Areeeeen/OW_Signalscope_Planet_Finder/firmware/v2.0/Signalscope_v2.0/astronomy.c

/*
    Astronomy Engine for C/C++.
    https://github.com/cosinekitty/astronomy

    MIT License

    Copyright (c) 2019-2025 Don Cross <cosinekitty@gmail.com>

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
    THE SOFTWARE IS PROVIDED "AS IS", WITHOUT WARRANTY OF ANY KIND, EXPRESS OR
    IMPLIED, INCLUDING BUT NOT LIMITED TO THE WARRANTIES OF MERCHANTABILITY,
    FITNESS FOR A PARTICULAR PURPOSE AND NONINFRINGEMENT. IN NO EVENT SHALL THE
    AUTHORS OR COPYRIGHT HOLDERS BE LIABLE FOR ANY CLAIM, DAMAGES OR OTHER
    LIABILITY, WHETHER IN AN ACTION OF CONTRACT, TORT OR OTHERWISE, ARISING FROM,
    OUT OF OR IN CONNECTION WITH THE SOFTWARE OR THE USE OR OTHER DEALINGS IN THE
    SOFTWARE.
*/

#include <math.h>
#include <stdint.h>
#include <stdio.h>
#include <stdlib.h>
#include <string.h>

#define ASTRONOMY_ENGINE_WHOLE_SECOND

#if !defined(ASTRONOMY_ENGINE_NO_CURRENT_TIME)
#if defined(__unix__) || defined(__unix) || (defined(__APPLE__) && defined(__MACH__))
#include <sys/time.h>
#elif defined(_WIN32)
#define WIN32_LEAN_AND_MEAN
#include <windows.h>
#else
#include <time.h>
#endif
#endif

#include "astronomy.h"

#ifdef __FAST_MATH__
#error Astronomy Engine does not support "fast math" optimization because it causes incorrect behavior. See: https://github.com/cosinekitty/astronomy/issues/245
#endif

#ifdef __cplusplus
extern "C" {
#endif

/** @cond DOXYGEN_SKIP */
#define PI      3.14159265358979323846

#define PLUTO_NUM_STATES  51
#define PLUTO_TIME_STEP   29200
#define PLUTO_DT          146

#define PLUTO_NSTEPS      201



typedef enum
{
    FROM_2000,
    INTO_2000
}
precess_dir_t;

typedef struct
{
    double x;
    double y;
    double z;
}
terse_vector_t;

typedef struct
{
    double          tt;   /* J2000 terrestrial time [days] */
    terse_vector_t  r;    /* position [au] */
    terse_vector_t  v;    /* velocity [au/day] */
    terse_vector_t  a;    /* acceleration [au/day^2] */
}
body_grav_calc_t;

typedef struct
{
    body_grav_calc_t   step[PLUTO_NSTEPS];
}
body_segment_t;

typedef struct
{
    double          tt;  /* Terrestrial Time in J2000 days */
    terse_vector_t  r;   /* position [au] */
    terse_vector_t  v;   /* velocity [au/day] */
}
body_state_t;

typedef struct
{
    body_state_t Sun;
    body_state_t Jupiter;
    body_state_t Saturn;
    body_state_t Uranus;
    body_state_t Neptune;
}
major_bodies_t;

typedef struct
{
    astro_time_t      time;
    body_state_t      gravitators[1 + BODY_SUN];
    body_grav_calc_t *bodies;
}
gravsim_endpoint_t;

struct astro_grav_sim_s
{
    astro_body_t        originBody;
    int                 numBodies;
    gravsim_endpoint_t  endpoint[2];
    gravsim_endpoint_t *prev;
    gravsim_endpoint_t *curr;
};

typedef struct
{
    double ra;
    double dec;
    double dist;
}
stardef_t;

/* Mean obliquity of the J2000 ecliptic in radians. */
#define OBLIQ_2000       0.40909260059599012
#define COS_OBLIQ_2000   0.9174821430670688
#define SIN_OBLIQ_2000   0.3977769691083922

/** @endcond */

#define NSTARS 8
static stardef_t StarTable[NSTARS];

#define GetStarPointer(body)    (((body) >= BODY_STAR1) && ((body) <= BODY_STAR8) ? &StarTable[(body) - BODY_STAR1] : NULL)

static const stardef_t *UserDefinedStar(astro_body_t body)
{
    const stardef_t *star = GetStarPointer(body);
    if (star != NULL && star->dist > 0.0)
        return star;
    return NULL;
}


/**
 * @brief Assign equatorial coordinates to a user-defined star.
 *
 * Some Astronomy Engine functions allow their `body` parameter to
 * be a user-defined fixed point in the sky, loosely called a "star".
 * This function assigns a right ascension, declination, and distance
 * to one of the eight user-defined stars `BODY_STAR1` .. `BODY_STAR8`.
 *
 * Stars are not valid until defined. Once defined, they retain their
 * definition until re-defined by another call to `Astronomy_DefineStar`.
 *
 * @param body
 *      One of the eight user-defined star identifiers: `BODY_STAR1` .. `BODY_STAR8`.
 *
 * @param ra
 *      The right ascension to be assigned to the star, expressed in J2000 equatorial coordinates (EQJ).
 *      The value is in units of sidereal hours, and must be within the half-open range [0, 24).
 *
 * @param dec
 *      The declination to be assigned to the star, expressed in J2000 equatorial coordinates (EQJ).
 *      The value is in units of degrees north (positive) or south (negative) of the J2000 equator,
 *      and must be within the closed range [-90, +90].
 *
 * @param distanceLightYears
 *      The distance between the star and the Sun, expressed in light-years.
 *      This value is used to calculate the tiny parallax shift as seen by an observer on Earth.
 *      If you don't know the distance to the star, using a large value like 1000 will generally work well.
 *      The minimum allowed distance is 1 light-year, which is required to provide certain internal optimizations.
 *
 * @return
 *      `ASTRO_SUCCESS` indicates the star has been defined. Any other value indicates an error,
 *      in which case no change has taken place to any of the star definitions.
 */
astro_status_t Astronomy_DefineStar(astro_body_t body, double ra, double dec, double distanceLightYears)
{
    stardef_t *star = GetStarPointer(body);

    if (star == NULL)
        return ASTRO_INVALID_BODY;

    if (!isfinite(ra) || ra < 0.0 || ra >= 24.0)
        return ASTRO_INVALID_PARAMETER;

    if (!isfinite(dec) || dec < -90.0 || dec > +90.0)
        return ASTRO_INVALID_PARAMETER;

    if (!isfinite(distanceLightYears) || distanceLightYears < 1.0)
        return ASTRO_INVALID_PARAMETER;

    star->ra   = ra;
    star->dec  = dec;
    star->dist = distanceLightYears * AU_PER_LY;

    return ASTRO_SUCCESS;
}

static const terse_vector_t VecZero = { 0.0, 0.0, 0.0 };

static terse_vector_t VecAdd(terse_vector_t a, terse_vector_t b)
{
    terse_vector_t c;
    c.x = a.x + b.x;
    c.y = a.y + b.y;
    c.z = a.z + b.z;
    return c;
}

static void VecIncr(terse_vector_t *target, terse_vector_t source)
{
    target->x += source.x;
    target->y += source.y;
    target->z += source.z;
}

static void VecDecr(terse_vector_t *target, terse_vector_t source)
{
    target->x -= source.x;
    target->y -= source.y;
    target->z -= source.z;
}

static terse_vector_t VecMul(double s, terse_vector_t v)
{
    terse_vector_t p;
    p.x = s * v.x;
    p.y = s * v.y;
    p.z = s * v.z;
    return p;
}

static void VecScale(terse_vector_t *target, double scalar)
{
    target->x *= scalar;
    target->y *= scalar;
    target->z *= scalar;
}

static terse_vector_t VecRamp(terse_vector_t a, terse_vector_t b, double ramp)
{
    terse_vector_t c;
    c.x = (1-ramp)*a.x + ramp*b.x;
    c.y = (1-ramp)*a.y + ramp*b.y;
    c.z = (1-ramp)*a.z + ramp*b.z;
    return c;
}

static terse_vector_t VecMean(terse_vector_t a, terse_vector_t b)
{
    terse_vector_t c;
    c.x = (a.x + b.x) / 2;
    c.y = (a.y + b.y) / 2;
    c.z = (a.z + b.z) / 2;
    return c;
}

static astro_state_vector_t ExportState(body_state_t terse, astro_time_t time)
{
    astro_state_vector_t state;

    state.status = ASTRO_SUCCESS;
    state.x  = terse.r.x;
    state.y  = terse.r.y;
    state.z  = terse.r.z;
    state.vx = terse.v.x;
    state.vy = terse.v.y;
    state.vz = terse.v.z;
    state.t  = time;

    return state;
}

static astro_state_vector_t ExportGravCalc(body_grav_calc_t calc, astro_time_t time)
{
    astro_state_vector_t state;

    state.status = ASTRO_SUCCESS;
    state.x  = calc.r.x;
    state.y  = calc.r.y;
    state.z  = calc.r.z;
    state.vx = calc.v.x;
    state.vy = calc.v.y;
    state.vz = calc.v.z;
    state.t  = time;

    return state;
}

static const double DAYS_PER_TROPICAL_YEAR = 365.24217;
static const double ASEC360 = 1296000.0;
static const double ASEC2RAD = 4.848136811095359935899141e-6;
static const double PI2 = 2.0 * PI;
static const double ARC = 3600.0 * 180.0 / PI;          /* arcseconds per radian */
static const double SECONDS_PER_DAY = 24.0 * 3600.0;
static const double SOLAR_DAYS_PER_SIDEREAL_DAY = 0.9972695717592592;
static const double MEAN_SYNODIC_MONTH = 29.530588;     /* average number of days for Moon to return to the same phase */
static const double EARTH_ORBITAL_PERIOD = 365.256;
static const double NEPTUNE_ORBITAL_PERIOD = 60189.0;

/*
    Degrees of refractive "lift" seen for objects near horizon.
    More precisely, the angle below the horizon a point has to be, at sea level,
    to appear to be exactly on the horizon.
    If the ground plane is higher than sea level, this angle
    needs to be corrected for decreased atmospheric density.
*/
static const double REFRACTION_NEAR_HORIZON = 34.0 / 60.0;


#define             SUN_RADIUS_AU  (SUN_RADIUS_KM / KM_PER_AU)

#define EARTH_MEAN_RADIUS_KM        6371.0            /* mean radius of the Earth's geoid, without atmosphere */
#define EARTH_ATMOSPHERE_KM           88.0            /* effective atmosphere thickness for lunar eclipses. see: https://eclipse.gsfc.nasa.gov/LEcat5/shadow.html */
#define EARTH_ECLIPSE_RADIUS_KM     (EARTH_MEAN_RADIUS_KM + EARTH_ATMOSPHERE_KM)
#define EARTH_EQUATORIAL_RADIUS_AU  (EARTH_EQUATORIAL_RADIUS_KM / KM_PER_AU)

#define MOON_MEAN_RADIUS_KM         1737.4
#define MOON_EQUATORIAL_RADIUS_AU   (MOON_EQUATORIAL_RADIUS_KM / KM_PER_AU)
#define MOON_POLAR_RADIUS_AU        (MOON_POLAR_RADIUS_KM / KM_PER_AU)

/* The inclination of the moon's rotation axis to the ecliptic plane, in radians. */
#define MOON_AXIS_INCLINATION_RADIANS    (DEG2RAD * 1.543)

static const double ASEC180 = 180.0 * 60.0 * 60.0;      /* arcseconds per 180 degrees (or pi radians) */
static const double EARTH_MOON_MASS_RATIO = 81.30056;

/*
    Masses of the Sun and planets, used for:
    (1) Calculating the Solar System Barycenter
    (2) Integrating the movement of Pluto

    https://web.archive.org/web/20120220062549/http://iau-comm4.jpl.nasa.gov/de405iom/de405iom.pdf

    Page 10 in the above document describes the constants used in the DE405 ephemeris.
    The following are GM values (gravity constant * mass) in [au^3 / day^2].
    This side-steps issues of not knowing the exact values of G and masses M[i];
    the products GM[i] are known extremely accurately.
*/
static const double SUN_GM     = 0.2959122082855911e-03;
static const double MERCURY_GM = 0.4912547451450812e-10;
static const double VENUS_GM   = 0.7243452486162703e-09;
static const double EARTH_GM   = 0.8887692390113509e-09;
static const double MARS_GM    = 0.9549535105779258e-10;
static const double JUPITER_GM = 0.2825345909524226e-06;
static const double SATURN_GM  = 0.8459715185680659e-07;
static const double URANUS_GM  = 0.1292024916781969e-07;
static const double NEPTUNE_GM = 0.1524358900784276e-07;
static const double PLUTO_GM   = 0.2188699765425970e-11;

#define MOON_GM   (EARTH_GM / EARTH_MOON_MASS_RATIO)

/** @cond DOXYGEN_SKIP */
#define ASTRO_ARRAYSIZE(x)    (sizeof(x) / sizeof(x[0]))
#define AU_PER_PARSEC   (ASEC180 / PI)             /* exact definition of how many AU = one parsec */
#define Y2000_IN_MJD    (T0 - MJD_BASIS)
/** @endcond */

static astro_ecliptic_t RotateEquatorialToEcliptic(const double pos[3], double obliq_radians, astro_time_t time);
static int QuadInterp(
    double tm, double dt, double fa, double fm, double fb,
    double *t, double *df_dt);

static double LongitudeOffset(double diff)
{
    double offset = diff;

    while (offset <= -180.0)
        offset += 360.0;

    while (offset > 180.0)
        offset -= 360.0;

    return offset;
}

static double NormalizeLongitude(double lon)
{
    while (lon < 0.0)
        lon += 360.0;

    while (lon >= 360.0)
        lon -= 360.0;

    return lon;
}

/**
 * @brief Calculates the length of the given vector.
 *
 * Calculates the non-negative length of the given vector.
 * The length is expressed in the same units as the vector's components,
 * usually astronomical units (AU).
 *
 * @param vector The vector whose length is to be calculated.
 * @return The length of the vector.
 */
double Astronomy_VectorLength(astro_vector_t vector)
{
    return sqrt(vector.x*vector.x + vector.y*vector.y + vector.z*vector.z);
}

/**
 * @brief Finds the name of a celestial body.
 * @param body The celestial body whose name is to be found.
 * @return The English-language name of the celestial body, or "" if the body is not valid.
 */
const char *Astronomy_BodyName(astro_body_t body)
{
    switch (body)
    {
    case BODY_MERCURY:  return "Mercury";
    case BODY_VENUS:    return "Venus";
    case BODY_EARTH:    return "Earth";
    case BODY_MARS:     return "Mars";
    case BODY_JUPITER:  return "Jupiter";
    case BODY_SATURN:   return "Saturn";
    case BODY_URANUS:   return "Uranus";
    case BODY_NEPTUNE:  return "Neptune";
    case BODY_PLUTO:    return "Pluto";
    case BODY_SUN:      return "Sun";
    case BODY_MOON:     return "Moon";
    case BODY_EMB:      return "EMB";
    case BODY_SSB:      return "SSB";
    default:            return "";
    }
}

/**
 * @brief Returns the #astro_body_t value corresponding to the given English name.
 * @param name One of the following strings: Sun, Moon, Mercury, Venus, Earth, Mars, Jupiter, Saturn, Uranus, Neptune, Pluto, EMB, SSB.
 * @return If `name` is one of the listed strings (case-sensitive), the returned value is the corresponding #astro_body_t value, otherwise it is `BODY_INVALID`.
 */
astro_body_t Astronomy_BodyCode(const char *name)
{
    if (name != NULL)
    {
        if (!strcmp(name, "Mercury"))   return BODY_MERCURY;
        if (!strcmp(name, "Venus"))     return BODY_VENUS;
        if (!strcmp(name, "Earth"))     return BODY_EARTH;
        if (!strcmp(name, "Mars"))      return BODY_MARS;
        if (!strcmp(name, "Jupiter"))   return BODY_JUPITER;
        if (!strcmp(name, "Saturn"))    return BODY_SATURN;
        if (!strcmp(name, "Uranus"))    return BODY_URANUS;
        if (!strcmp(name, "Neptune"))   return BODY_NEPTUNE;
        if (!strcmp(name, "Pluto"))     return BODY_PLUTO;
        if (!strcmp(name, "Sun"))       return BODY_SUN;
        if (!strcmp(name, "Moon"))      return BODY_MOON;
        if (!strcmp(name, "EMB"))       return BODY_EMB;
        if (!strcmp(name, "SSB"))       return BODY_SSB;
    }
    return BODY_INVALID;
}

/**
 * @brief Returns 1 for planets that are farther from the Sun than the Earth is, 0 otherwise.
 */
static int IsSuperiorPlanet(astro_body_t body)
{
    switch (body)
    {
    case BODY_MARS:
    case BODY_JUPITER:
    case BODY_SATURN:
    case BODY_URANUS:
    case BODY_NEPTUNE:
    case BODY_PLUTO:
        return 1;

    default:
        return 0;
    }
}

/**
 * @brief Returns the average number of days it takes for a planet to orbit the Sun.
 * @param body One of the planets: Mercury, Venus, Earth, Mars, Jupiter, Saturn, Uranus, Neptune, or Pluto.
 * @return The mean orbital period of the body, or 0.0 if the `body` parameter is not valid.
 */
double Astronomy_PlanetOrbitalPeriod(astro_body_t body)
{
    switch (body)
    {
    case BODY_MERCURY:  return     87.969;
    case BODY_VENUS:    return    224.701;
    case BODY_EARTH:    return    EARTH_ORBITAL_PERIOD;
    case BODY_MARS:     return    686.980;
    case BODY_JUPITER:  return   4332.589;
    case BODY_SATURN:   return  10759.22;
    case BODY_URANUS:   return  30685.4;
    case BODY_NEPTUNE:  return  NEPTUNE_ORBITAL_PERIOD;
    case BODY_PLUTO:    return  90560.0;
    default:            return  0.0;        /* invalid body */
    }
}

static astro_vector_t VecError(astro_status_t status, astro_time_t time)
{
    astro_vector_t vec;
    vec.x = vec.y = vec.z = NAN;
    vec.t = time;
    vec.status = status;
    return vec;
}

static astro_state_vector_t StateVecError(astro_status_t status, astro_time_t time)
{
    astro_state_vector_t vec;
    vec.x = vec.y = vec.z = NAN;
    vec.vx = vec.vy = vec.vz = NAN;
    vec.t = time;
    vec.status = status;
    return vec;
}

static astro_spherical_t SphereError(astro_status_t status)
{
    astro_spherical_t sphere;
    sphere.status = status;
    sphere.dist = sphere.lat = sphere.lon = NAN;
    return sphere;
}

static astro_time_t TimeError(void)
{
    astro_time_t time;
    time.tt = time.ut = time.eps = time.psi = time.st = NAN;
    return time;
}

static astro_equatorial_t EquError(astro_status_t status)
{
    astro_equatorial_t equ;
    equ.vec = VecError(status, TimeError());
    equ.ra = equ.dec = equ.dist = NAN;
    equ.status = status;
    return equ;
}

static astro_ecliptic_t EclError(astro_status_t status)
{
    astro_ecliptic_t ecl;
    ecl.status = status;
    ecl.elon = ecl.elat = NAN;
    ecl.vec = VecError(status, TimeError());
    return ecl;
}

static astro_angle_result_t AngleError(astro_status_t status)
{
    astro_angle_result_t result;
    result.status = status;
    result.angle = NAN;
    return result;
}

static astro_func_result_t FuncError(astro_status_t status)
{
    astro_func_result_t result;
    result.status = status;
    result.value = NAN;
    return result;
}

static astro_rotation_t RotationErr(astro_status_t status)
{
    astro_rotation_t rotation;
    int i, j;

    rotation.status = status;
    for (i=0; i<3; ++i)
        for (j=0; j<3; ++j)
            rotation.rot[i][j] = NAN;

    return rotation;
}

static astro_moon_quarter_t MoonQuarterError(astro_status_t status)
{
    astro_moon_quarter_t result;
    result.status = status;
    result.quarter = -1;
    result.time = TimeError();
    return result;
}

static astro_elongation_t ElongError(astro_status_t status)
{
    astro_elongation_t result;

    result.status = status;
    result.elongation = NAN;
    result.ecliptic_separation = NAN;
    result.time = TimeError();
    result.visibility = (astro_visibility_t)(-1);

    return result;
}

static astro_hour_angle_t HourAngleError(astro_status_t status)
{
    astro_hour_angle_t result;

    result.status = status;
    result.time = TimeError();
    result.hor.altitude = result.hor.azimuth = result.hor.dec = result.hor.ra = NAN;

    return result;
}

static astro_illum_t IllumError(astro_status_t status)
{
    astro_illum_t result;

    result.status = status;
    result.time = TimeError();
    result.mag = NAN;
    result.phase_angle = NAN;
    result.phase_fraction = NAN;
    result.helio_dist = NAN;
    result.ring_tilt = NAN;

    return result;
}

static astro_apsis_t ApsisError(astro_status_t status)
{
    astro_apsis_t result;

    result.status = status;
    result.time = TimeError();
    result.kind = APSIS_INVALID;
    result.dist_km = result.dist_au = NAN;

    return result;
}

static astro_search_result_t SearchError(astro_status_t status)
{
    astro_search_result_t result;
    result.time = TimeError();
    result.status = status;
    return result;
}

static astro_constellation_t ConstelErr(astro_status_t status)
{
    astro_constellation_t constel;
    constel.status = status;
    constel.symbol = constel.name = NULL;
    constel.ra_1875 = constel.dec_1875 = NAN;
    return constel;
}

static astro_transit_t TransitErr(astro_status_t status)
{
    astro_transit_t transit;
    transit.status = status;
    transit.start = transit.peak = transit.finish = TimeError();
    transit.separation = NAN;
    return transit;
}

static astro_axis_t AxisErr(astro_status_t status, astro_time_t time)
{
    astro_axis_t axis;
    axis.status = status;
    axis.ra = axis.dec = axis.spin = NAN;
    axis.north = VecError(status, time);
    return axis;
}

static astro_func_result_t SynodicPeriod(astro_body_t body)
{
    double Tp;                         /* planet's orbital period in days */
    astro_func_result_t result;

    /* The Earth does not have a synodic period as seen from itself. */
    if (body == BODY_EARTH)
        return FuncError(ASTRO_EARTH_NOT_ALLOWED);

    if (body == BODY_MOON)
    {
        result.status = ASTRO_SUCCESS;
        result.value = MEAN_SYNODIC_MONTH;
        return result;
    }

    Tp = Astronomy_PlanetOrbitalPeriod(body);
    if (Tp <= 0.0)
        return FuncError(ASTRO_INVALID_BODY);

    result.status = ASTRO_SUCCESS;
    result.value = fabs(EARTH_ORBITAL_PERIOD / (EARTH_ORBITAL_PERIOD/Tp - 1.0));
    return result;
}


/**
 * @brief Calculates the angle between two vectors.
 *
 * Given a pair of vectors, this function returns the angle in degrees
 * between the two vectors in 3D space.
 * The angle is measured in the plane that contains both vectors.
 *
 * @param a
 *      The first vector.
 *
 * @param b
 *      The second vector.
 *
 * @returns
 *      On success, the `status` field holds `ASTRO_SUCCESS` and `angle` holds
 *      a number of degrees in the range [0, 180].
 *      If either vector has a zero magnitude or contains NAN (not a number)
 *      components, the `status` will hold the error code `ASTRO_BAD_VECTOR`.
 */
astro_angle_result_t Astronomy_AngleBetween(astro_vector_t a, astro_vector_t b)
{
    double r, dot;
    astro_angle_result_t result;

    r = Astronomy_VectorLength(a) * Astronomy_VectorLength(b);
    if (r < 1.0e-8 || !isfinite(r))
        return AngleError(ASTRO_BAD_VECTOR);

    dot = (a.x*b.x + a.y*b.y + a.z*b.z) / r;

    if (dot <= -1.0)
        result.angle = 180.0;
    else if (dot >= +1.0)
        result.angle = 0.0;
    else
        result.angle = RAD2DEG * acos(dot);

    result.status = ASTRO_SUCCESS;
    return result;
}

/**
 * @brief The default Delta T function used by Astronomy Engine.
 *
 * Espenak and Meeus use a series of piecewise polynomials to
 * approximate DeltaT of the Earth in their "Five Millennium Canon of Solar Eclipses".
 * See: https://eclipse.gsfc.nasa.gov/SEhelp/deltatpoly2004.html
 * This is the default Delta T function used by Astronomy Engine.
 *
 * @param ut
 *      The floating point number of days since noon UTC on January 1, 2000.
 *
 * @returns
 *      The estimated difference TT-UT on the given date, expressed in seconds.
 */
double Astronomy_DeltaT_EspenakMeeus(double ut)
{
    double y, u, u2, u3, u4, u5, u6, u7;

    /*
        Fred Espenak writes about Delta-T generically here:
        https://eclipse.gsfc.nasa.gov/SEhelp/deltaT.html
        https://eclipse.gsfc.nasa.gov/SEhelp/deltat2004.html

        He provides polynomial approximations for distant years here:
        https://eclipse.gsfc.nasa.gov/SEhelp/deltatpoly2004.html

        They start with a year value 'y' such that y=2000 corresponds
        to the UTC Date 15-January-2000. Convert difference in days
        to mean tropical years.
    */

    y = 2000 + ((ut - 14) / DAYS_PER_TROPICAL_YEAR);

    if (y < -500)
    {
        u = (y - 1820) / 100;
        return -20 + (32 * u*u);
    }
    if (y < 500)
    {
        u = y / 100;
        u2 = u*u; u3 = u*u2; u4 = u2*u2; u5 = u2*u3; u6 = u3*u3;
        return 10583.6 - 1014.41*u + 33.78311*u2 - 5.952053*u3 - 0.1798452*u4 + 0.022174192*u5 + 0.0090316521*u6;
    }
    if (y < 1600)
    {
        u = (y - 1000) / 100;
        u2 = u*u; u3 = u*u2; u4 = u2*u2; u5 = u2*u3; u6 = u3*u3;
        return 1574.2 - 556.01*u + 71.23472*u2 + 0.319781*u3 - 0.8503463*u4 - 0.005050998*u5 + 0.0083572073*u6;
    }
    if (y < 1700)
    {
        u = y - 1600;
        u2 = u*u; u3 = u*u2;
        return 120 - 0.9808*u - 0.01532*u2 + u3/7129.0;
    }
    if (y < 1800)
    {
        u = y - 1700;
        u2 = u*u; u3 = u*u2; u4 = u2*u2;
        return 8.83 + 0.1603*u - 0.0059285*u2 + 0.00013336*u3 - u4/1174000;
    }
    if (y < 1860)
    {
        u = y - 1800;
        u2 = u*u; u3 = u*u2; u4 = u2*u2; u5 = u2*u3; u6 = u3*u3; u7 = u3*u4;
        return 13.72 - 0.332447*u + 0.0068612*u2 + 0.0041116*u3 - 0.00037436*u4 + 0.0000121272*u5 - 0.0000001699*u6 + 0.000000000875*u7;
    }
    if (y < 1900)
    {
        u = y - 1860;
        u2 = u*u; u3 = u*u2; u4 = u2*u2; u5 = u2*u3;
        return 7.62 + 0.5737*u - 0.251754*u2 + 0.01680668*u3 - 0.0004473624*u4 + u5/233174;
    }
    if (y < 1920)
    {
        u = y - 1900;
        u2 = u*u; u3 = u*u2; u4 = u2*u2;
        return -2.79 + 1.494119*u - 0.0598939*u2 + 0.0061966*u3 - 0.000197*u4;
    }
    if (y < 1941)
    {
        u = y - 1920;
        u2 = u*u; u3 = u*u2;
        return 21.20 + 0.84493*u - 0.076100*u2 + 0.0020936*u3;
    }
    if (y < 1961)
    {
        u = y - 1950;
        u2 = u*u; u3 = u*u2;
        return 29.07 + 0.407*u - u2/233 + u3/2547;
    }
    if (y < 1986)
    {
        u = y - 1975;
        u2 = u*u; u3 = u*u2;
        return 45.45 + 1.067*u - u2/260 - u3/718;
    }
    if (y < 2005)
    {
        u = y - 2000;
        u2 = u*u; u3 = u*u2; u4 = u2*u2; u5 = u2*u3;
        return 63.86 + 0.3345*u - 0.060374*u2 + 0.0017275*u3 + 0.000651814*u4 + 0.00002373599*u5;
    }
    if (y < 2050)
    {
        u = y - 2000;
        return 62.92 + 0.32217*u + 0.005589*u*u;
    }
    if (y < 2150)
    {
        u = (y-1820)/100;
        return -20 + 32*u*u - 0.5628*(2150 - y);
    }

    /* all years after 2150 */
    u = (y - 1820) / 100;
    return -20 + (32 * u*u);
}

/**
 * @brief A Delta T function that approximates the one used by the JPL Horizons tool.
 *
 * In order to support unit tests based on data generated by the JPL Horizons online
 * tool, I had to reverse engineer their Delta T function by generating a table that
 * contained it. The main difference between their tool and the Espenak/Meeus function
 * is that they stop extrapolating the Earth's deceleration after the year 2017.
 *
 * @param ut
 *      The floating point number of days since noon UTC on January 1, 2000.
 *
 * @returns
 *      The estimated difference TT-UT on the given date, expressed in seconds.
 */
double Astronomy_DeltaT_JplHorizons(double ut)
{
    if (ut > 17.0 * DAYS_PER_TROPICAL_YEAR)
        ut = 17.0 * DAYS_PER_TROPICAL_YEAR;

    return Astronomy_DeltaT_EspenakMeeus(ut);
}

static astro_deltat_func DeltaTFunc = Astronomy_DeltaT_EspenakMeeus;

/**
 * @brief Changes the function Astronomy Engine uses to calculate Delta T.
 *
 * Most programs should not call this function. It is for advanced use cases only.
 * By default, Astronomy Engine uses the function #Astronomy_DeltaT_EspenakMeeus
 * to estimate changes in the Earth's rotation rate over time.
 * However, for the sake of unit tests that compare calculations against
 * external data sources that use alternative models for Delta T,
 * it is sometimes useful to replace the Delta T model to match.
 * This function allows replacing the Delta T model with any other
 * desired model.
 *
 * @param func
 *      A pointer to a function to convert UT values to DeltaT values.
 */
void Astronomy_SetDeltaTFunction(astro_deltat_func func)
{
    DeltaTFunc = func;
}

static double TerrestrialTime(double ut)
{
    return ut + DeltaTFunc(ut)/86400.0;
}

/**
 * @brief Converts a J2000 day value to an #astro_time_t value.
 *
 * This function can be useful for reproducing an #astro_time_t structure
 * from its `ut` field only.
 *
 * @param ut
 *      The floating point number of days since noon UTC on January 1, 2000.
 *      This time is based on UTC/UT1 civil time.
 *      See #Astronomy_TerrestrialTime if you instead want to create
 *      a time value based on atomic Terrestrial Time (TT).
 *
 * @returns
 *      An #astro_time_t value for the given `ut` value.
 */
astro_time_t Astronomy_TimeFromDays(double ut)
{
    astro_time_t  time;
    time.ut = ut;
    time.tt = TerrestrialTime(ut);
    time.psi = time.eps = time.st = NAN;
    return time;
}


/**
 * @brief Converts a terrestrial time value into an #astro_time_t value.
 *
 * This function can be used in rare cases where a time must be based
 * on Terrestrial Time (TT) rather than Universal Time (UT).
 * Most developers will want to call #Astronomy_TimeFromDays instead of
 * this function, because usually time is based on civil time adjusted
 * by leap seconds to match the Earth's rotation, rather than the uniformly
 * flowing TT used to calculate solar system dynamics. In rare cases
 * where the caller already knows TT, this function is provided to create
 * an #astro_time_t value that can be passed to Astronomy Engine functions.
 *
 * @param tt
 *      The floating point number of days of uniformly flowing
 *      Terrestrial Time since the J2000 epoch.
 *
 * @returns
 *      An #astro_time_t value for the given `tt` value.
 */
astro_time_t Astronomy_TerrestrialTime(double tt)
{
    /* Iterate to solve to find the correct ut for a given tt, and create an astro_time_t for that time. */
    astro_time_t time = Astronomy_TimeFromDays(tt);
    for(;;)
    {
        double err = tt - time.tt;
        if (fabs(err) < 1.0e-12)
            return time;
        time = Astronomy_AddDays(time, err);
    }
}

#if !defined(ASTRONOMY_ENGINE_NO_CURRENT_TIME)
/**
 * @brief Returns the computer's current date and time in the form of an #astro_time_t.
 *
 * Uses the computer's system clock to find the current UTC date and time.
 * Converts that date and time to an #astro_time_t value and returns the result.
 * Callers can pass this value to other Astronomy Engine functions to calculate
 * current observational conditions.
 *
 * On supported platforms (Linux/Unix, Mac, Windows), the time is measured with
 * microsecond resolution.
 *
 * On unsupported platforms, a compiler error will occur due to lack of
 * microsecond resolution support. However, if whole second resolution is good
 * enough for your application, you can define the preprocessor symbol
 * `ASTRONOMY_ENGINE_WHOLE_SECOND` to use the portable function `time(NULL)`.
 * Alternatively, if you do not need to use `Astronomy_CurrentTime`, you can
 * define the preprocessor symbol `ASTRONOMY_ENGINE_NO_CURRENT_TIME` to
 * exclude this function from your code.
 */
astro_time_t Astronomy_CurrentTime(void)
{
    astro_time_t t;
    double sec;         /* Seconds since midnight January 1, 1970. */

#if defined(__unix__) || defined(__unix) || (defined(__APPLE__) && defined(__MACH__))
    struct timeval tv;
    gettimeofday(&tv, NULL);
    sec = (double)tv.tv_sec + tv.tv_usec/1.0e+6;
#elif defined(_WIN32)
    FILETIME ft;
    ULARGE_INTEGER large;
    /* Get time in 100-nanosecond units from January 1, 1601. */
    GetSystemTimePreciseAsFileTime(&ft);
    large.u.LowPart  = ft.dwLowDateTime;
    large.u.HighPart = ft.dwHighDateTime;
    sec = (large.QuadPart - 116444736000000000ULL) / 1.0e+7;
#elif defined(ASTRONOMY_ENGINE_WHOLE_SECOND)
    sec = time(NULL);
#else
    #error Microsecond time resolution is not supported on this platform. Define ASTRONOMY_ENGINE_WHOLE_SECOND to use second resolution instead.
#endif

    /* Convert seconds to days, then subtract to get days since noon on January 1, 2000. */
    t.ut = (sec / SECONDS_PER_DAY) - 10957.5;
    t.tt = TerrestrialTime(t.ut);
    t.psi = t.eps = t.st = NAN;
    return t;
}
#endif

/**
 * @brief Creates an #astro_time_t value from a given calendar date and time.
 *
 * Given a UTC calendar date and time, calculates an #astro_time_t value that can
 * be passed to other Astronomy Engine functions for performing various calculations
 * relating to that date and time.
 *
 * It is the caller's responsibility to ensure that the parameter values are correct.
 * The parameters are not checked for validity,
 * and this function never returns any indication of an error.
 * Invalid values, for example passing in February 31, may cause unexpected return values.
 *
 * @param year      The UTC calendar year, e.g. 2019.
 * @param month     The UTC calendar month in the range 1..12.
 * @param day       The UTC calendar day in the range 1..31.
 * @param hour      The UTC hour of the day in the range 0..23.
 * @param minute    The UTC minute in the range 0..59.
 * @param second    The UTC floating-point second in the range [0, 60).
 *
 * @return  An #astro_time_t value that represents the given calendar date and time.
 */
astro_time_t Astronomy_MakeTime(int year, int month, int day, int hour, int minute, double second)
{
    astro_time_t time;
    int64_t y = (int64_t)year;
    int64_t m = (int64_t)month;
    int64_t d = (int64_t)day;
    int64_t f = (14 - m) / 12;

    /*
        This formula is adapted from NOVAS C 3.1 function julian_date(),
        which in turn comes from Henry F. Fliegel & Thomas C. Van Flendern:
        Communications of the ACM, Vol 11, No 10, October 1968, p. 657.
        See: https://dl.acm.org/doi/pdf/10.1145/364096.364097

        [Don Cross - 2023-02-25] I modified the formula so that it will
        work correctly with years as far back as -999999.
    */
    int64_t y2000 = (
        (d - 365972956)
        + (1461*(y + 1000000 - f))/4
        + (367*(m - 2 + 12*f))/12
        - (3*((y + 1000100 - f) / 100))/4
    );

    time.ut = (y2000 - 0.5) + (hour / 24.0) + (minute / 1440.0) + (second / 86400.0);
    time.tt = TerrestrialTime(time.ut);
    time.psi = time.eps = time.st = NAN;

    return time;
}

/**
 * @brief   Calculates the sum or difference of an #astro_time_t with a specified floating point number of days.
 *
 * Sometimes we need to adjust a given #astro_time_t value by a certain amount of time.
 * This function adds the given real number of days in `days` to the date and time in `time`.
 *
 * More precisely, the result's Universal Time field `ut` is exactly adjusted by `days` and
 * the Terrestrial Time field `tt` is adjusted correctly for the resulting UTC date and time,
 * according to the historical and predictive Delta-T model provided by the
 * [United States Naval Observatory](http://maia.usno.navy.mil/ser7/).
 *
 * The value stored in `time` will not be modified; it is passed by value.
 *
 * @param time  A date and time for which to calculate an adjusted date and time.
 * @param days  A floating point number of days by which to adjust `time`. May be negative, 0, or positive.
 * @return  A date and time that is conceptually equal to `time + days`.
 */
astro_time_t Astronomy_AddDays(astro_time_t time, double days)
{
    /*
        This is slightly wrong, but the error is tiny.
        We really should be adding to TT, not to UT.
        But using TT would require creating an inverse function for DeltaT,
        which would be quite a bit of extra calculation.
        I estimate the error is in practice on the order of 10^(-7)
        times the value of 'days'.
        This is based on a typical drift of 1 second per year between UT and TT.
    */

    astro_time_t sum;

    sum.ut = time.ut + days;
    sum.tt = TerrestrialTime(sum.ut);
    sum.eps = sum.psi = sum.st = NAN;

    return sum;
}

/**
 * @brief   Creates an #astro_time_t value from a given calendar date and time.
 *
 * This function is similar to #Astronomy_MakeTime, only it receives a
 * UTC calendar date and time in the form of an #astro_utc_t structure instead of
 * as separate numeric parameters.  Astronomy_TimeFromUtc is the inverse of
 * #Astronomy_UtcFromTime.
 *
 * @param utc   The UTC calendar date and time to be converted to #astro_time_t.
 * @return  A value that can be used for astronomical calculations for the given date and time.
 */
astro_time_t Astronomy_TimeFromUtc(astro_utc_t utc)
{
    return Astronomy_MakeTime(utc.year, utc.month, utc.day, utc.hour, utc.minute, utc.second);
}

/**
 * @brief Determines the calendar year, month, day, and time from an #astro_time_t value.
 *
 * After calculating the date and time of an astronomical event in the form of
 * an #astro_time_t value, it is often useful to display the result in a human-readable
 * form. This function converts the linear time scales in the `ut` field of #astro_time_t
 * into a calendar date and time: year, month, day, hours, minutes, and seconds, expressed
 * in UTC.
 *
 * @param time  The astronomical time value to be converted to calendar date and time.
 * @return  A date and time broken out into conventional year, month, day, hour, minute, and second.
 */
astro_utc_t Astronomy_UtcFromTime(astro_time_t time)
{
    /* Adapted from the NOVAS C 3.1 function cal_date() */
    astro_utc_t utc;
    int64_t jd, k, m, n;
    double djd, x;
    const int64_t c = 2500;

    djd = time.ut + 2451545.5;
    jd = (int64_t)floor(djd);

    x = 24.0 * fmod(djd, 1.0);
    if (x < 0.0)
        x += 24.0;
    utc.hour = (int)x;
    x = 60.0 * fmod(x, 1.0);
    utc.minute = (int)x;
    utc.second = 60.0 * fmod(x, 1.0);

    /*
        This is my own adjustment to the NOVAS cal_date logic
        so that it can handle dates much farther back in the past.
        I add c*400 years worth of days at the front,
        then subtract c*400 years at the back,
        which avoids negative values in the formulas that mess up
        the calendar date calculations.
        Any multiple of 400 years has the same number of days,
        because it eliminates all the special cases for leap years.
    */
    k = jd + (68569 + c*146097);
    n = (4 * k) / 146097;
    k = k - (146097 * n + 3)/4;
    m = (4000 * (k+1)) / 1461001;
    k = k - (1461 * m)/4 + 31;

    utc.month = (int) ((80 * k) / 2447);
    utc.day = (int) (k - (2447*utc.month)/80);
    k = utc.month / 11;

    utc.month = (int) (utc.month + 2 - 12*k);
    utc.year = (int) (100 * (n - 49) + m + k - 400*c);

    return utc;
}


/**
 * @brief Formats an #astro_time_t value as an ISO 8601 string.
 *
 * Given an #astro_time_t value `time`, formats it as an ISO 8601
 * string to the resolution specified by the `format` parameter.
 * The result is stored in the `text` buffer whose capacity in bytes
 * is specified by `size`.
 *
 * @param time
 *      The date and time whose civil time `time.ut` is to be formatted as an ISO 8601 string.
 *      If the civil time is outside the year range -999999 to +999999, the function fails
 *      and returns `ASTRO_BAD_TIME`. Years prior to 1583 are treated as if they are
 *      using the modern Gregorian calendar, even when the Julian calendar was actually in effect.
 *      The year before 1 AD, commonly known as 1 BC, is represented by the value 0.
 *      The year 2 BC is represented by -1, etc.
 *
 * @param format
 *      Specifies the resolution to which the date and time should be formatted,
 *      as explained at #astro_time_format_t.
 *      If the value of `format` is not recognized, the function fails and
 *      returns `ASTRO_INVALID_PARAMETER`.
 *
 * @param text
 *      A pointer to a text buffer to receive the output.
 *      If `text` is `NULL`, this function returns `ASTRO_INVALID_PARAMETER`.
 *      If the function fails for any reason, and `text` is not `NULL`,
 *      and `size` is greater than 0, the `text` buffer is set to an empty string.
 *
 * @param size
 *      The size in bytes of the buffer pointed to by `text`. The buffer must
 *      be large enough to accomodate the output format selected by the
 *      `format` parameter, as specified at #astro_time_format_t.
 *      If `size` is too small to hold the string as specified by `format`,
 *      the `text` buffer is set to `""` (if possible)
 *      and the function returns `ASTRO_BUFFER_TOO_SMALL`.
 *      A buffer that is `TIME_TEXT_BYTES` (28) bytes or larger is always large enough for this function.
 *
 * @return `ASTRO_SUCCESS` on success; otherwise an error as described in the parameter notes.
 */
astro_status_t Astronomy_FormatTime(
    astro_time_t time,
    astro_time_format_t format,
    char *text,
    size_t size)
{
    int nprinted;
    double rounding;
    size_t min_size;
    astro_utc_t utc;
    char ytext[20];   /* worst case: "+999999" = 8 characters including terminal '\0'. But gcc 12.2 still complains! */

    if (text == NULL)
        return ASTRO_INVALID_PARAMETER;

    if (size == 0)
        return ASTRO_BUFFER_TOO_SMALL;

    text[0] = '\0';     /* initialize to empty string, in case an error occurs */

    /* Validate 'size' parameter and perform date/time rounding. */
    switch (format)
    {
    case TIME_FORMAT_DAY:
        min_size = 11;                          /* "2020-12-31" */
        rounding = 0.0;                         /* no rounding */
        break;

    case TIME_FORMAT_MINUTE:
        min_size = 18;                          /* "2020-12-31T15:47Z" */
        rounding = 0.5 / (24.0 * 60.0);         /* round to nearest minute */
        break;

    case TIME_FORMAT_SECOND:
        min_size = 21;                          /* "2020-12-31T15:47:59Z" */
        rounding = 0.5 / (24.0 * 3600.0);       /* round to nearest second */
        break;

    case TIME_FORMAT_MILLI:
        min_size = 25;                          /* "2020-12-31T15:47:59.123Z" */
        rounding = 0.5 / (24.0 * 3600000.0);    /* round to nearest millisecond */
        break;

    default:
        return ASTRO_INVALID_PARAMETER;
    }

    /* Perform rounding. */
    time.ut += rounding;

    /* Convert linear J2000 days to Gregorian UTC date/time. */
    utc = Astronomy_UtcFromTime(time);
    if (utc.year < -999999 || utc.year > +999999)
        return ASTRO_BAD_TIME;

    if (utc.year < 0)
    {
        snprintf(ytext, sizeof(ytext), "-%06d", -utc.year);
        min_size += 3;  /* '-' prefix and two extra year digits. */
    }
    else if (utc.year <= 9999)
    {
        snprintf(ytext, sizeof(ytext), "%04d", utc.year);
    }
    else
    {
        snprintf(ytext, sizeof(ytext), "+%06d", utc.year);
        min_size += 3;  /* '+' prefix and two extra year digits. */
    }

    /* Check for insufficient buffer size. */
    if (size < min_size)
        return ASTRO_BUFFER_TOO_SMALL;

    /* Format the string. */
    switch (format)
    {
    case TIME_FORMAT_DAY:
        nprinted = snprintf(text, size, "%s-%02d-%02d",
            ytext, utc.month, utc.day);
        break;

    case TIME_FORMAT_MINUTE:
        nprinted = snprintf(text, size, "%s-%02d-%02dT%02d:%02dZ",
            ytext, utc.month, utc.day,
            utc.hour, utc.minute);
        break;

    case TIME_FORMAT_SECOND:
        nprinted = snprintf(text, size, "%s-%02d-%02dT%02d:%02d:%02.0lfZ",
            ytext, utc.month, utc.day,
            utc.hour, utc.minute, floor(utc.second));
        break;

    case TIME_FORMAT_MILLI:
        nprinted = snprintf(text, size, "%s-%02d-%02dT%02d:%02d:%06.3lfZ",
            ytext, utc.month, utc.day,
            utc.hour, utc.minute, floor(1000.0 * utc.second) / 1000.0);
        break;

    default:
        /* We should have already failed for any unknown 'format' value. */
        return ASTRO_INTERNAL_ERROR;
    }

    if (nprinted < 0)
        return ASTRO_INTERNAL_ERROR;    /* should not be possible for snprintf to return a negative number */

    if ((size_t)(1+nprinted) != min_size)
        return ASTRO_INTERNAL_ERROR;    /* there must be a bug calculating min_size or formatting the string */

    return ASTRO_SUCCESS;
}


/**
 * @brief   Creates an observer object that represents a location on or near the surface of the Earth.
 *
 * Some Astronomy Engine functions calculate values pertaining to an observer on the Earth.
 * These functions require a value of type #astro_observer_t that represents the location
 * of such an observer.
 *
 * @param latitude      The geographic latitude of the observer in degrees north (positive) or south (negative) of the equator.
 * @param longitude     The geographic longitude of the observer in degrees east (positive) or west (negative) of the prime meridian at Greenwich, England.
 * @param height        The height of the observer in meters above mean sea level.
 * @return An observer object that can be passed to astronomy functions that require a geographic location.
 */
astro_observer_t Astronomy_MakeObserver(double latitude, double longitude, double height)
{
    astro_observer_t observer;

    observer.latitude = latitude;
    observer.longitude = longitude;
    observer.height = height;

    return observer;
}

static void iau2000b(astro_time_t *time)
{
    /* Truncated and hand-optimized nutation model. */

    if ((time != NULL) && isnan(time->psi))
    {
        double t, elp, f, d, om, arg, dp, de, sarg, carg;

        t = time->tt / 36525.0;
        elp = fmod(1287104.79305 + t * 129596581.0481,  ASEC360) * ASEC2RAD;
        f   = fmod(335779.526232 + t * 1739527262.8478, ASEC360) * ASEC2RAD;
        d   = fmod(1072260.70369 + t * 1602961601.2090, ASEC360) * ASEC2RAD;
        om  = fmod(450160.398036 - t * 6962890.5431,    ASEC360) * ASEC2RAD;

        sarg = sin(om);
        carg = cos(om);
        dp = (-172064161.0 - 174666.0*t)*sarg + 33386.0*carg;
        de = (92052331.0 + 9086.0*t)*carg + 15377.0*sarg;

        arg = 2.0*(f - d + om);
        sarg = sin(arg);
        carg = cos(arg);
        dp += (-13170906.0 - 1675.0*t)*sarg - 13696.0*carg;
        de += (5730336.0 - 3015.0*t)*carg - 4587.0*sarg;

        arg = 2.0*(f + om);
        sarg = sin(arg);
        carg = cos(arg);
        dp += (-2276413.0 - 234.0*t)*sarg + 2796.0*carg;
        de += (978459.0 - 485.0*t)*carg + 1374.0*sarg;

        arg = 2.0*om;
        sarg = sin(arg);
        carg = cos(arg);
        dp += (2074554.0 + 207.0*t)*sarg - 698.0*carg;
        de += (-897492.0 + 470.0*t)*carg - 291.0*sarg;

        sarg = sin(elp);
        carg = cos(elp);
        dp += (1475877.0 - 3633.0*t)*sarg + 11817.0*carg;
        de += (73871.0 - 184.0*t)*carg - 1924.0*sarg;

        time->psi = -0.000135 + (dp * 1.0e-7);
        time->eps = +0.000388 + (de * 1.0e-7);
    }
}

static double mean_obliq(double tt)
{
    double t = tt / 36525.0;
    double asec =
        (((( -  0.0000000434   * t
             -  0.000000576  ) * t
             +  0.00200340   ) * t
             -  0.0001831    ) * t
             - 46.836769     ) * t + 84381.406;

    return asec / 3600.0;
}

/** @cond DOXYGEN_SKIP */
typedef struct
{
    double tt;
    double dpsi;
    double deps;
    double ee;
    double mobl;
    double tobl;
}
earth_tilt_t;
/** @endcond */

static earth_tilt_t e_tilt(astro_time_t *time)
{
    earth_tilt_t et;

    /* There is no good answer for what to do if time==NULL. Callers must prevent! */

    iau2000b(time);
    et.dpsi = time->psi;
    et.deps = time->eps;
    et.mobl = mean_obliq(time->tt);
    et.tobl = et.mobl + (et.deps / 3600.0);
    et.tt = time->tt;
    et.ee = et.dpsi * cos(et.mobl * DEG2RAD) / 15.0;

    return et;
}

static void obl_ecl2equ_vec(double obl, astro_time_t time, const double ecl[3], double equ[3])
{
    double obl_rad = obl * DEG2RAD;
    double cos_obl = cos(obl_rad);
    double sin_obl = sin(obl_rad);

    equ[0] = ecl[0];
    equ[1] = ecl[1]*cos_obl - ecl[2]*sin_obl;
    equ[2] = ecl[1]*sin_obl + ecl[2]*cos_obl;
}

static void ecl2equ_vec(astro_time_t time, const double ecl[3], double equ[3])
{
    double obl = mean_obliq(time.tt);
    obl_ecl2equ_vec(obl, time, ecl, equ);
}

static astro_rotation_t precession_rot(astro_time_t time, precess_dir_t dir)
{
    /*
        dir==INTO_2000: converts mean equator of date (EQM) to J2000 mean equator (EQJ).
        dir==FROM_2000: converts J2000 mean equator (EQJ) to mean equator of date (EQM).
    */

    astro_rotation_t rotation;
    double xx, yx, zx, xy, yy, zy, xz, yz, zz;
    double t, psia, omegaa, chia, sa, ca, sb, cb, sc, cc, sd, cd;
    double eps0 = 84381.406;

    t = time.tt / 36525;

    psia   = (((((-    0.0000000951  * t
                 +    0.000132851 ) * t
                 -    0.00114045  ) * t
                 -    1.0790069   ) * t
                 + 5038.481507    ) * t);

    omegaa = (((((+    0.0000003337  * t
                 -    0.000000467 ) * t
                 -    0.00772503  ) * t
                 +    0.0512623   ) * t
                 -    0.025754    ) * t + eps0);

    chia   = (((((-    0.0000000560  * t
                 +    0.000170663 ) * t
                 -    0.00121197  ) * t
                 -    2.3814292   ) * t
                 +   10.556403    ) * t);

    eps0 = eps0 * ASEC2RAD;
    psia = psia * ASEC2RAD;
    omegaa = omegaa * ASEC2RAD;
    chia = chia * ASEC2RAD;

    sa = sin(eps0);
    ca = cos(eps0);
    sb = sin(-psia);
    cb = cos(-psia);
    sc = sin(-omegaa);
    cc = cos(-omegaa);
    sd = sin(chia);
    cd = cos(chia);

    xx =  cd * cb - sb * sd * cc;
    yx =  cd * sb * ca + sd * cc * cb * ca - sa * sd * sc;
    zx =  cd * sb * sa + sd * cc * cb * sa + ca * sd * sc;
    xy = -sd * cb - sb * cd * cc;
    yy = -sd * sb * ca + cd * cc * cb * ca - sa * cd * sc;
    zy = -sd * sb * sa + cd * cc * cb * sa + ca * cd * sc;
    xz =  sb * sc;
    yz = -sc * cb * ca - sa * cc;
    zz = -sc * cb * sa + cc * ca;

    if (dir == INTO_2000)
    {
        /* Perform rotation from other epoch to J2000.0. */
        rotation.rot[0][0] = xx;
        rotation.rot[0][1] = yx;
        rotation.rot[0][2] = zx;
        rotation.rot[1][0] = xy;
        rotation.rot[1][1] = yy;
        rotation.rot[1][2] = zy;
        rotation.rot[2][0] = xz;
        rotation.rot[2][1] = yz;
        rotation.rot[2][2] = zz;
    }
    else
    {
        /* Perform rotation from J2000.0 to other epoch. */
        rotation.rot[0][0] = xx;
        rotation.rot[0][1] = xy;
        rotation.rot[0][2] = xz;
        rotation.rot[1][0] = yx;
        rotation.rot[1][1] = yy;
        rotation.rot[1][2] = yz;
        rotation.rot[2][0] = zx;
        rotation.rot[2][1] = zy;
        rotation.rot[2][2] = zz;
    }

    rotation.status = ASTRO_SUCCESS;
    return rotation;
}


static void rotate(const double invec[3], const double rot[3][3], double outvec[3])
{
    outvec[0] = rot[0][0]*invec[0] + rot[1][0]*invec[1] + rot[2][0]*invec[2];
    outvec[1] = rot[0][1]*invec[0] + rot[1][1]*invec[1] + rot[2][1]*invec[2];
    outvec[2] = rot[0][2]*invec[0] + rot[1][2]*invec[1] + rot[2][2]*invec[2];
}

static void precession(
    const double pos1[3],
    astro_time_t time,
    precess_dir_t dir,
    double pos2[3])
{
    astro_rotation_t r = precession_rot(time, dir);
    rotate(pos1, r.rot, pos2);
}

static void precession_posvel(
    const double pos1[3],
    const double vel1[3],
    astro_time_t time,
    precess_dir_t dir,
    double pos2[3],
    double vel2[3])
{
    astro_rotation_t r = precession_rot(time, dir);
    rotate(pos1, r.rot, pos2);
    rotate(vel1, r.rot, vel2);
}


static astro_equatorial_t vector2radec(const double pos[3], astro_time_t time)
{
    astro_equatorial_t equ;
    double xyproj;

    /* Copy the cartesian coordinates from the input into the returned structure. */
    equ.vec.status = ASTRO_SUCCESS;
    equ.vec.t = time;
    equ.vec.x = pos[0];
    equ.vec.y = pos[1];
    equ.vec.z = pos[2];

    /* Calculate spherical coordinates: RA, DEC, distance. */
    xyproj = pos[0]*pos[0] + pos[1]*pos[1];
    equ.dist = sqrt(xyproj + pos[2]*pos[2]);
    equ.status = ASTRO_SUCCESS;
    if (xyproj == 0.0)
    {
        if (pos[2] == 0.0)
        {
            /* Indeterminate coordinates; pos vector has zero length. */
            equ = EquError(ASTRO_BAD_VECTOR);
        }
        else if (pos[2] < 0)
        {
            equ.ra = 0.0;
            equ.dec = -90.0;
        }
        else
        {
            equ.ra = 0.0;
            equ.dec = +90.0;
        }
    }
    else
    {
        equ.ra = RAD2HOUR * atan2(pos[1], pos[0]);
        if (equ.ra < 0)
            equ.ra += 24.0;

        equ.dec = RAD2DEG * atan2(pos[2], sqrt(xyproj));
    }

    return equ;
}


static astro_rotation_t nutation_rot(astro_time_t *time, precess_dir_t dir)
{
    /*
        Creates a rotation matrix that adds/removes nutation from
        an equatorial vector of date:

        The `dir` parameter is a little misleading, but reflects the
        common task of working together with precession_rot() to
        convert mean equator of 2000 to/from true equator of date.
        Here is the actual result of `dir`:

        dir==INTO_2000: Subtract nutation from true equator of date (EQD)
        to produce mean equator of date (EQM).

        dir==FROM_2000: Add nutation from mean equator of date (EQM) to
        produce true equator of date (EQD).
    */

    astro_rotation_t rotation;
    earth_tilt_t tilt;
    double oblm, oblt, psi, cobm, sobm, cobt, sobt, cpsi, spsi;
    double xx, yx, zx, xy, yy, zy, xz, yz, zz;

    if (time == NULL)
        return RotationErr(ASTRO_INVALID_PARAMETER);

    tilt = e_tilt(time);
    oblm = tilt.mobl * DEG2RAD;
    oblt = tilt.tobl * DEG2RAD;
    psi = tilt.dpsi * ASEC2RAD;
    cobm = cos(oblm);
    sobm = sin(oblm);
    cobt = cos(oblt);
    sobt = sin(oblt);
    cpsi = cos(psi);
    spsi = sin(psi);

    xx = cpsi;
    yx = -spsi * cobm;
    zx = -spsi * sobm;
    xy = spsi * cobt;
    yy = cpsi * cobm * cobt + sobm * sobt;
    zy = cpsi * sobm * cobt - cobm * sobt;
    xz = spsi * sobt;
    yz = cpsi * cobm * sobt - sobm * cobt;
    zz = cpsi * sobm * sobt + cobm * cobt;

    if (dir == FROM_2000)
    {
        /* convert J2000 to of-date */
        rotation.rot[0][0] = xx;
        rotation.rot[0][1] = xy;
        rotation.rot[0][2] = xz;
        rotation.rot[1][0] = yx;
        rotation.rot[1][1] = yy;
        rotation.rot[1][2] = yz;
        rotation.rot[2][0] = zx;
        rotation.rot[2][1] = zy;
        rotation.rot[2][2] = zz;
    }
    else
    {
        /* convert of-date to J2000 */
        rotation.rot[0][0] = xx;
        rotation.rot[0][1] = yx;
        rotation.rot[0][2] = zx;
        rotation.rot[1][0] = xy;
        rotation.rot[1][1] = yy;
        rotation.rot[1][2] = zy;
        rotation.rot[2][0] = xz;
        rotation.rot[2][1] = yz;
        rotation.rot[2][2] = zz;
    }

    rotation.status = ASTRO_SUCCESS;
    return rotation;
}

static void nutation(
    const double inpos[3],
    astro_time_t *time,
    precess_dir_t dir,
    double outpos[3])
{
    astro_rotation_t r = nutation_rot(time, dir);
    rotate(inpos, r.rot, outpos);
}

static void nutation_posvel(
    const double inpos[3],
    const double invel[3],
    astro_time_t *time,
    precess_dir_t dir,
    double outpos[3],
    double outvel[3])
{
    astro_rotation_t r = nutation_rot(time, dir);
    rotate(inpos, r.rot, outpos);
    rotate(invel, r.rot, outvel);
}

static double era(double ut)        /* Earth Rotation Angle */
{
    double thet1 = 0.7790572732640 + 0.00273781191135448 * ut;
    double thet3 = fmod(ut, 1.0);
    double theta = 360.0 * fmod(thet1 + thet3, 1.0);
    if (theta < 0.0)
        theta += 360.0;

    return theta;
}

/**
 * @brief Calculates Greenwich Apparent Sidereal Time (GAST).
 *
 * Given a date and time, this function calculates the rotation of the
 * Earth, represented by the equatorial angle of the Greenwich prime meridian
 * with respect to distant stars (not the Sun, which moves relative to background
 * stars by almost one degree per day).
 * This angle is called Greenwich Apparent Sidereal Time (GAST).
 * GAST is measured in sidereal hours in the half-open range [0, 24).
 * When GAST = 0, it means the prime meridian is aligned with the of-date equinox,
 * corrected at that time for precession and nutation of the Earth's axis.
 * In this context, the "equinox" is the direction in space where the Earth's
 * orbital plane (the ecliptic) intersects with the plane of the Earth's equator,
 * at the location on the Earth's orbit of the (seasonal) March equinox.
 * As the Earth rotates, GAST increases from 0 up to 24 sidereal hours,
 * then starts over at 0.
 * To convert to degrees, multiply the return value by 15.
 *
 * @param time
 *      The date and time for which to find GAST.
 *      The parameter is passed by address because it can be modified by the call:
 *      As an optimization, this function caches the sidereal time value in `time`,
 *      unless it has already been cached, in which case the cached value is reused.
 *      If the `time` pointer is NULL, this function returns a NAN value.
 *
 * @returns {number}
 */
double Astronomy_SiderealTime(astro_time_t *time)
{
    if (time == NULL)
        return NAN;

    if (isnan(time->st))
    {
        double t = time->tt / 36525.0;
        double eqeq = 15.0 * e_tilt(time).ee;    /* Replace with eqeq=0 to get GMST instead of GAST (if we ever need it) */
        double theta = era(time->ut);
        double st = (eqeq + 0.014506 +
            (((( -    0.0000000368   * t
                -    0.000029956  ) * t
                -    0.00000044   ) * t
                +    1.3915817    ) * t
                + 4612.156534     ) * t);

        double gst = fmod(st/3600.0 + theta, 360.0) / 15.0;
        if (gst < 0.0)
            gst += 24.0;

        time->st = gst;
    }

    return time->st;     /* return sidereal hours in the half-open range [0, 24). */
}

static astro_observer_t inverse_terra(const double ovec[3], double st)
{
    double x, y, z, p, F, W, D, c, s, c2, s2;
    double lon_deg, lat_deg, lat, radicand, factor, denom, adjust;
    double height_km, stlocl, distance_au;
    astro_observer_t observer;
    int count;

    /* Convert from AU to kilometers. */
    x = ovec[0] * KM_PER_AU;
    y = ovec[1] * KM_PER_AU;
    z = ovec[2] * KM_PER_AU;
    p = hypot(x, y);
    if (p < 1.0e-6)
    {
        /* Special case: within 1 millimeter of a pole! */
        /* Use arbitrary longitude, and latitude determined by polarity of z. */
        lon_deg = 0.0;
        lat_deg = (z > 0.0) ? +90.0 : -90.0;
        /* Elevation is calculated directly from z */
        height_km = fabs(z) - EARTH_POLAR_RADIUS_KM;
    }
    else
    {
        stlocl = atan2(y, x);
        /* Calculate exact longitude. */
        lon_deg = RAD2DEG*stlocl - (15.0 * st);
        /* Normalize longitude to the range (-180, +180]. */
        while (lon_deg <= -180.0)
            lon_deg += 360.0;
        while (lon_deg > +180.0)
            lon_deg -= 360.0;
        /* Numerically solve for exact latitude, using Newton's Method. */
        F = EARTH_FLATTENING * EARTH_FLATTENING;
        /* Start with initial latitude estimate, based on a spherical Earth. */
        lat = atan2(z, p);
        distance_au = sqrt(ovec[0]*ovec[0] + ovec[1]*ovec[1] + ovec[2]*ovec[2]);
        if (distance_au < 1.0)
            distance_au = 1.0;
        for (count = 0; ; ++count)
        {
            if (count > 10)
            {
                fprintf(stderr, "\nFATAL(inverse_terra): did not converge!\n");
                exit(1);
            }

            /* Calculate the error function W(lat). */
            /* We try to find the root of W, meaning where the error is 0. */
            c = cos(lat);
            s = sin(lat);
            factor = (F-1)*EARTH_EQUATORIAL_RADIUS_KM;
            c2 = c*c;
            s2 = s*s;
            radicand = c2 + F*s2;
            denom = sqrt(radicand);
            W = (factor*s*c)/denom - z*c + p*s;
            if (fabs(W) < distance_au * 2.0e-8)
                break;  /* The error is now negligible. */
            /* Error is still too large. Find the next estimate. */
            /* Calculate D = the derivative of W with respect to lat. */
            D = factor*((c2 - s2)/denom - s2*c2*(F-1)/(factor*radicand)) + z*s + p*c;
            lat -= W/D;
        }
        /* We now have a solution for the latitude in radians. */
        lat_deg = lat * RAD2DEG;
        /* Solve for exact height in meters. */
        /* There are two formulas I can use. Use whichever has the less risky denominator. */
        adjust = EARTH_EQUATORIAL_RADIUS_KM / denom;
        if (fabs(s) > fabs(c))
            height_km = z/s - F*adjust;
        else
            height_km = p/c - adjust;
    }

    observer.latitude = lat_deg;
    observer.longitude = lon_deg;
    observer.height = 1000.0 * height_km;
    return observer;
}

static void terra(astro_observer_t observer, double st, double pos[3], double vel[3])
{
    static const double ANGVEL = 7.2921150e-5;

    double phi = observer.latitude * DEG2RAD;
    double sinphi = sin(phi);
    double cosphi = cos(phi);
    double c = 1.0 / hypot(cosphi, sinphi*EARTH_FLATTENING);
    double s = c * (EARTH_FLATTENING * EARTH_FLATTENING);
    double ht_km = observer.height / 1000.0;
    double ach = EARTH_EQUATORIAL_RADIUS_KM*c + ht_km;
    double ash = EARTH_EQUATORIAL_RADIUS_KM*s + ht_km;
    double stlocl = (15.0*st + observer.longitude) * DEG2RAD;
    double sinst = sin(stlocl);
    double cosst = cos(stlocl);

    if (pos != NULL)
    {
        pos[0] = ach * cosphi * cosst / KM_PER_AU;
        pos[1] = ach * cosphi * sinst / KM_PER_AU;
        pos[2] = ash * sinphi / KM_PER_AU;
    }

    if (vel != NULL)
    {
        vel[0] = -(ANGVEL * 86400.0 / KM_PER_AU) * ach * cosphi * sinst;
        vel[1] = +(ANGVEL * 86400.0 / KM_PER_AU) * ach * cosphi * cosst;
        vel[2] = 0.0;
    }
}

static void geo_pos(astro_time_t *time, astro_observer_t observer, double pos[3])
{
    double gast;
    double pos1[3], pos2[3];

    if (time == NULL)
    {
        pos[0] = pos[1] = pos[2] = NAN;
    }
    else
    {
        gast = Astronomy_SiderealTime(time);
        terra(observer, gast, pos1, NULL);
        nutation(pos1, time, INTO_2000, pos2);
        precession(pos2, *time, INTO_2000, pos);
    }
}

static void spin(double angle, const double pos1[3], double vec2[3])
{
    double angr = angle * DEG2RAD;
    double cosang = cos(angr);
    double sinang = sin(angr);
    vec2[0] = +cosang*pos1[0] + sinang*pos1[1];
    vec2[1] = -sinang*pos1[0] + cosang*pos1[1];
    vec2[2] = pos1[2];
}

/*------------------ CalcMoon ------------------*/

/** @cond DOXYGEN_SKIP */

#define DECLARE_PASCAL_ARRAY_1(elemtype,name,xmin,xmax) \
    elemtype name[(xmax)-(xmin)+1]

#define DECLARE_PASCAL_ARRAY_2(elemtype,name,xmin,xmax,ymin,ymax) \
    elemtype name[(xmax)-(xmin)+1][(ymax)-(ymin)+1]

#define ACCESS_PASCAL_ARRAY_1(name,xmin,x) \
    ((name)[(x)-(xmin)])

#define ACCESS_PASCAL_ARRAY_2(name,xmin,ymin,x,y) \
    ((name)[(x)-(xmin)][(y)-(ymin)])

typedef struct
{
    double t;
    double dgam;
    double dlam, n, gam1c, sinpi;
    double l0, l, ls, f, d, s;
    double dl0, dl, dls, df, dd, ds;
    DECLARE_PASCAL_ARRAY_2(double,co,-6,6,1,4);   /* ARRAY[-6..6,1..4] OF REAL */
    DECLARE_PASCAL_ARRAY_2(double,si,-6,6,1,4);   /* ARRAY[-6..6,1..4] OF REAL */
}
MoonContext;

#define T           (ctx->t)
#define DGAM        (ctx->dgam)
#define DLAM        (ctx->dlam)
#define N           (ctx->n)
#define GAM1C       (ctx->gam1c)
#define SINPI       (ctx->sinpi)
#define L0          (ctx->l0)
#define L           (ctx->l)
#define LS          (ctx->ls)
#define F           (ctx->f)
#define D           (ctx->d)
#define S           (ctx->s)
#define DL0         (ctx->dl0)
#define DL          (ctx->dl)
#define DLS         (ctx->dls)
#define DF          (ctx->df)
#define DD          (ctx->dd)
#define DS          (ctx->ds)
#define CO(x,y)     ACCESS_PASCAL_ARRAY_2(ctx->co,-6,1,x,y)
#define SI(x,y)     ACCESS_PASCAL_ARRAY_2(ctx->si,-6,1,x,y)

static double Frac(double x)
{
    return x - floor(x);
}

static void AddThe(
    double c1, double s1, double c2, double s2,
    double *c, double *s)
{
    *c = c1*c2 - s1*s2;
    *s = s1*c2 + c1*s2;
}

static double Sine(double phi)
{
    /* sine, of phi in revolutions, not radians */
    return sin(PI2 * phi);
}

static void LongPeriodic(MoonContext *ctx)
{
    double S1 = Sine(0.19833+0.05611*T);
    double S2 = Sine(0.27869+0.04508*T);
    double S3 = Sine(0.16827-0.36903*T);
    double S4 = Sine(0.34734-5.37261*T);
    double S5 = Sine(0.10498-5.37899*T);
    double S6 = Sine(0.42681-0.41855*T);
    double S7 = Sine(0.14943-5.37511*T);

    DL0 = 0.84*S1+0.31*S2+14.27*S3+ 7.26*S4+ 0.28*S5+0.24*S6;
    DL  = 2.94*S1+0.31*S2+14.27*S3+ 9.34*S4+ 1.12*S5+0.83*S6;
    DLS =-6.40*S1                                   -1.89*S6;
    DF  = 0.21*S1+0.31*S2+14.27*S3-88.70*S4-15.30*S5+0.24*S6-1.86*S7;
    DD  = DL0-DLS;
    DGAM  = -3332E-9 * Sine(0.59734-5.37261*T)
             -539E-9 * Sine(0.35498-5.37899*T)
              -64E-9 * Sine(0.39943-5.37511*T);
}

static void Init(MoonContext *ctx)
{
    int I, J, MAX;
    double T2, ARG, FAC;

    T2 = T*T;
    DLAM = 0;
    DS = 0;
    GAM1C = 0;
    SINPI = 3422.7000;
    LongPeriodic(ctx);
    L0 = PI2*Frac(0.60643382+1336.85522467*T-0.00000313*T2) + DL0/ARC;
    L  = PI2*Frac(0.37489701+1325.55240982*T+0.00002565*T2) + DL /ARC;
    LS = PI2*Frac(0.99312619+  99.99735956*T-0.00000044*T2) + DLS/ARC;
    F  = PI2*Frac(0.25909118+1342.22782980*T-0.00000892*T2) + DF /ARC;
    D  = PI2*Frac(0.82736186+1236.85308708*T-0.00000397*T2) + DD /ARC;
    for (I=1; I<=4; ++I)
    {
        switch(I)
        {
            case 1:  ARG=L;  MAX=4; FAC=1.000002208;               break;
            case 2:  ARG=LS; MAX=3; FAC=0.997504612-0.002495388*T; break;
            case 3:  ARG=F;  MAX=4; FAC=1.000002708+139.978*DGAM;  break;
            default: ARG=D;  MAX=6; FAC=1.0;                       break;
        }
        CO(0,I) = 1.0;
        CO(1,I) = cos(ARG)*FAC;
        SI(0,I) = 0.0;
        SI(1,I) = sin(ARG)*FAC;
        for (J=2; J<=MAX; ++J)
            AddThe(CO(J-1,I), SI(J-1,I), CO(1,I), SI(1,I), &CO(J,I), &SI(J,I));

        for (J=1; J<=MAX; ++J)
        {
            CO(-J,I) =  CO(J,I);
            SI(-J,I) = -SI(J,I);
        }
    }
}

static void Term(const MoonContext *ctx, int p, int q, int r, int s, double *x, double *y)
{
    int k;
    DECLARE_PASCAL_ARRAY_1(int, i, 1, 4);
    #define I(n) ACCESS_PASCAL_ARRAY_1(i,1,n)

    I(1) = p;
    I(2) = q;
    I(3) = r;
    I(4) = s;
    *x = 1.0;
    *y = 0.0;

    for (k=1; k<=4; ++k)
        if (I(k) != 0.0)
            AddThe(*x, *y, CO(I(k), k), SI(I(k), k), x, y);

    #undef I
}

static void AddSol(
    MoonContext *ctx,
    double coeffl,
    double coeffs,
    double coeffg,
    double coeffp,
    int p,
    int q,
    int r,
    int s)
{
    double x, y;
    Term(ctx, p, q, r, s, &x, &y);
    DLAM += coeffl*y;
    DS += coeffs*y;
    GAM1C += coeffg*x;
    SINPI += coeffp*x;
}

#define ADDN(coeffn,p,q,r,s)    ( Term(ctx, (p),(q),(r),(s),&x,&y), (N += (coeffn)*y) )

static void SolarN(MoonContext *ctx)
{
    double x, y;

    N = 0.0;
    ADDN(-526.069, 0, 0,1,-2);
    ADDN(  -3.352, 0, 0,1,-4);
    ADDN( +44.297,+1, 0,1,-2);
    ADDN(  -6.000,+1, 0,1,-4);
    ADDN( +20.599,-1, 0,1, 0);
    ADDN( -30.598,-1, 0,1,-2);
    ADDN( -24.649,-2, 0,1, 0);
    ADDN(  -2.000,-2, 0,1,-2);
    ADDN( -22.571, 0,+1,1,-2);
    ADDN( +10.985, 0,-1,1,-2);
}

static void Planetary(MoonContext *ctx)
{
    DLAM +=
        +0.82*Sine(0.7736  -62.5512*T)+0.31*Sine(0.0466 -125.1025*T)
        +0.35*Sine(0.5785  -25.1042*T)+0.66*Sine(0.4591+1335.8075*T)
        +0.64*Sine(0.3130  -91.5680*T)+1.14*Sine(0.1480+1331.2898*T)
        +0.21*Sine(0.5918+1056.5859*T)+0.44*Sine(0.5784+1322.8595*T)
        +0.24*Sine(0.2275   -5.7374*T)+0.28*Sine(0.2965   +2.6929*T)
        +0.33*Sine(0.3132   +6.3368*T);
}

int _CalcMoonCount;     /* Undocumented global for performance tuning. */

static void CalcMoon(
    double centuries_since_j2000,
    double *geo_eclip_lon,      /* (LAMBDA) equinox of date */
    double *geo_eclip_lat,      /* (BETA)   equinox of date */
    double *distance_au)        /* (R) */
{
    double lat_seconds;
    MoonContext context;
    MoonContext *ctx = &context;    /* goofy, but makes macros work inside this function */

    context.t = centuries_since_j2000;
    Init(ctx);

    AddSol(ctx,    13.9020,    14.0600,    -0.0010,     0.2607, 0, 0, 0, 4);
    AddSol(ctx,     0.4030,    -4.0100,     0.3940,     0.0023, 0, 0, 0, 3);
    AddSol(ctx,  2369.9120,  2373.3600,     0.6010,    28.2333, 0, 0, 0, 2);
    AddSol(ctx,  -125.1540,  -112.7900,    -0.7250,    -0.9781, 0, 0, 0, 1);
    AddSol(ctx,     1.9790,     6.9800,    -0.4450,     0.0433, 1, 0, 0, 4);
    AddSol(ctx,   191.9530,   192.7200,     0.0290,     3.0861, 1, 0, 0, 2);
    AddSol(ctx,    -8.4660,   -13.5100,     0.4550,    -0.1093, 1, 0, 0, 1);
    AddSol(ctx, 22639.5000, 22609.0700,     0.0790,   186.5398, 1, 0, 0, 0);
    AddSol(ctx,    18.6090,     3.5900,    -0.0940,     0.0118, 1, 0, 0,-1);
    AddSol(ctx, -4586.4650, -4578.1300,    -0.0770,    34.3117, 1, 0, 0,-2);
    AddSol(ctx,     3.2150,     5.4400,     0.1920,    -0.0386, 1, 0, 0,-3);
    AddSol(ctx,   -38.4280,   -38.6400,     0.0010,     0.6008, 1, 0, 0,-4);
    AddSol(ctx,    -0.3930,    -1.4300,    -0.0920,     0.0086, 1, 0, 0,-6);
    AddSol(ctx,    -0.2890,    -1.5900,     0.1230,    -0.0053, 0, 1, 0, 4);
    AddSol(ctx,   -24.4200,   -25.1000,     0.0400,    -0.3000, 0, 1, 0, 2);
    AddSol(ctx,    18.0230,    17.9300,     0.0070,     0.1494, 0, 1, 0, 1);
    AddSol(ctx,  -668.1460,  -126.9800,    -1.3020,    -0.3997, 0, 1, 0, 0);
    AddSol(ctx,     0.5600,     0.3200,    -0.0010,    -0.0037, 0, 1, 0,-1);
    AddSol(ctx,  -165.1450,  -165.0600,     0.0540,     1.9178, 0, 1, 0,-2);
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
    AddSol(ctx,    -0.9920,    -0.0200,     0.0000,     0.0000, 1, 0, 2, 2);
    AddSol(ctx,   -45.0990,    -0.0200,     0.0000,    -0.0010, 1, 0, 2, 0);
    AddSol(ctx,    -0.1790,    -9.5200,     0.0000,    -0.0833, 1, 0, 2,-2);
    AddSol(ctx,    -0.3010,    -0.3300,     0.0000,     0.0014, 1, 0, 2,-4);
    AddSol(ctx,    -6.3820,    -3.3700,     0.0000,    -0.0481, 1, 0,-2, 2);
    AddSol(ctx,    39.5280,    85.1300,     0.0000,    -0.7136, 1, 0,-2, 0);
    AddSol(ctx,     9.3660,     0.7100,     0.0000,    -0.0112, 1, 0,-2,-2);
    AddSol(ctx,     0.2020,     0.0200,     0.0000,     0.0000, 1, 0,-2,-4);
    AddSol(ctx,     0.4150,     0.1000,     0.0000,     0.0013, 0, 1, 2, 0);
    AddSol(ctx,    -2.1520,    -2.2600,     0.0000,    -0.0066, 0, 1, 2,-2);
    AddSol(ctx,    -1.4400,    -1.3000,     0.0000,     0.0014, 0, 1,-2, 2);
    AddSol(ctx,     0.3840,    -0.0400,     0.0000,     0.0000, 0, 1,-2,-2);
    AddSol(ctx,     1.9380,     3.6000,    -0.1450,     0.0401, 4, 0, 0, 0);
    AddSol(ctx,    -0.9520,    -1.5800,     0.0520,    -0.0130, 4, 0, 0,-2);
    AddSol(ctx,    -0.5510,    -0.9400,     0.0320,    -0.0097, 3, 1, 0, 0);
    AddSol(ctx,    -0.4820,    -0.5700,     0.0050,    -0.0045, 3, 1, 0,-2);
    AddSol(ctx,     0.6810,     0.9600,    -0.0260,     0.0115, 3,-1, 0, 0);
    AddSol(ctx,    -0.2970,    -0.2700,     0.0020,    -0.0009, 2, 2, 0,-2);
    AddSol(ctx,     0.2540,     0.2100,    -0.0030,     0.0000, 2,-2, 0,-2);
    AddSol(ctx,    -0.2500,    -0.2200,     0.0040,     0.0014, 1, 3, 0,-2);
    AddSol(ctx,    -3.9960,     0.0000,     0.0000,     0.0004, 2, 0, 2, 0);
    AddSol(ctx,     0.5570,    -0.7500,     0.0000,    -0.0090, 2, 0, 2,-2);
    AddSol(ctx,    -0.4590,    -0.3800,     0.0000,    -0.0053, 2, 0,-2, 2);
    AddSol(ctx,    -1.2980,     0.7400,     0.0000,     0.0004, 2, 0,-2, 0);
    AddSol(ctx,     0.5380,     1.1400,     0.0000,    -0.0141, 2, 0,-2,-2);
    AddSol(ctx,     0.2630,     0.0200,     0.0000,     0.0000, 1, 1, 2, 0);
    AddSol(ctx,     0.4260,     0.0700,     0.0000,    -0.0006, 1, 1,-2,-2);
    AddSol(ctx,    -0.3040,     0.0300,     0.0000,     0.0003, 1,-1, 2, 0);
    AddSol(ctx,    -0.3720,    -0.1900,     0.0000,    -0.0027, 1,-1,-2, 2);
    AddSol(ctx,     0.4180,     0.0000,     0.0000,     0.0000, 0, 0, 4, 0);
    AddSol(ctx,    -0.3300,    -0.0400,     0.0000,     0.0000, 3, 0, 2, 0);

    SolarN(ctx);
    Planetary(ctx);
    S = F + DS/ARC;

    lat_seconds = (1.000002708 + 139.978*DGAM)*(18518.511+1.189+GAM1C)*sin(S)-6.24*sin(3*S) + N;

    *geo_eclip_lon = PI2 * Frac((L0+DLAM/ARC) / PI2);
    *geo_eclip_lat = lat_seconds * (DEG2RAD / 3600.0);
    *distance_au = (ARC * EARTH_EQUATORIAL_RADIUS_AU) / (0.999953253 * SINPI);
    ++_CalcMoonCount;
}

#undef T
#undef DGAM
#undef DLAM
#undef N
#undef GAM1C
#undef SINPI
#undef L0
#undef L
#undef LS
#undef F
#undef D
#undef S
#undef DL0
#undef DL
#undef DLS
#undef DF
#undef DD
#undef DS
#undef CO
#undef SI

/** @endcond */

/**
 * @brief Calculates equatorial geocentric position of the Moon at a given time.
 *
 * Given a time of observation, calculates the Moon's position as a vector.
 * The vector gives the location of the Moon's center relative to the Earth's center
 * with x-, y-, and z-components measured in astronomical units.
 * The coordinates are oriented with respect to the Earth's equator at the J2000 epoch.
 * In Astronomy Engine, this orientation is called EQJ.
 *
 * This algorithm is based on the Nautical Almanac Office's *Improved Lunar Ephemeris* of 1954,
 * which in turn derives from E. W. Brown's lunar theories from the early twentieth century.
 * It is adapted from Turbo Pascal code from the book
 * [Astronomy on the Personal Computer](https://www.springer.com/us/book/9783540672210)
 * by Montenbruck and Pfleger.
 *
 * To calculate ecliptic spherical coordinates instead, see #Astronomy_EclipticGeoMoon.
 *
 * @param time  The date and time for which to calculate the Moon's position.
 * @return The Moon's position as a vector in J2000 Cartesian equatorial (EQJ) coordinates.
 */
astro_vector_t Astronomy_GeoMoon(astro_time_t time)
{
    double geo_eclip_lon, geo_eclip_lat, distance_au;
    double dist_cos_lat;
    astro_vector_t vector;
    double gepos[3];
    double mpos1[3];
    double mpos2[3];

    CalcMoon(time.tt / 36525.0, &geo_eclip_lon, &geo_eclip_lat, &distance_au);

    /* Convert geocentric ecliptic spherical coordinates to Cartesian coordinates. */
    dist_cos_lat = distance_au * cos(geo_eclip_lat);
    gepos[0] = dist_cos_lat * cos(geo_eclip_lon);
    gepos[1] = dist_cos_lat * sin(geo_eclip_lon);
    gepos[2] = distance_au * sin(geo_eclip_lat);

    /* Convert ecliptic coordinates to equatorial coordinates, both in mean equinox of date. */
    ecl2equ_vec(time, gepos, mpos1);

    /* Convert equatorial coordinates from mean equinox of date to J2000 mean equinox. */
    precession(mpos1, time, INTO_2000, mpos2);

    vector.status = ASTRO_SUCCESS;
    vector.x = mpos2[0];
    vector.y = mpos2[1];
    vector.z = mpos2[2];
    vector.t = time;
    return vector;
}


/**
 * @brief Calculates spherical ecliptic geocentric position of the Moon.
 *
 * Given a time of observation, calculates the Moon's geocentric position
 * in ecliptic spherical coordinates. Provides the ecliptic latitude and
 * longitude in degrees, and the geocentric distance in astronomical units (AU).
 *
 * The ecliptic angles are measured in "ECT": relative to the true ecliptic plane and
 * equatorial plane at the specified time. This means the Earth's equator
 * is corrected for precession and nutation, and the plane of the Earth's
 * orbit is corrected for gradual obliquity drift.
 *
 * This algorithm is based on the Nautical Almanac Office's *Improved Lunar Ephemeris* of 1954,
 * which in turn derives from E. W. Brown's lunar theories from the early twentieth century.
 * It is adapted from Turbo Pascal code from the book
 * [Astronomy on the Personal Computer](https://www.springer.com/us/book/9783540672210)
 * by Montenbruck and Pfleger.
 *
 * To calculate a J2000 mean equator vector instead, use #Astronomy_GeoMoon.
 *
 * @param time  The date and time for which to calculate the Moon's position.
 * @return The Moon's position expressed in ecliptic coordinates using the true equinox of date (ECT).
 */
astro_spherical_t Astronomy_EclipticGeoMoon(astro_time_t time)
{
    astro_spherical_t sphere;
    astro_ecliptic_t eclip;
    earth_tilt_t et;
    double dist_cos_lat, ecm[3], eqm[3], eqd[3];

    /* CalcMoon produces ecliptic coordinates in mean equinox of date (ECM). */
    CalcMoon(time.tt / 36525.0, &sphere.lon, &sphere.lat, &sphere.dist);

    /* Calculate vector in ecliptic coordinates (ECM). */
    dist_cos_lat = sphere.dist * cos(sphere.lat);
    ecm[0] = dist_cos_lat * cos(sphere.lon);
    ecm[1] = dist_cos_lat * sin(sphere.lon);
    ecm[2] = sphere.dist * sin(sphere.lat);

    /* Obtain true and mean obliquity angles for the given time. */
    /* This serves to pre-calculate the nutation also, and cache it in `time`. */
    et = e_tilt(&time);

    /* Convert ecliptic coordinates to equatorial coordinates, both in mean equinox of date. */
    /* In other words, convert ECM to EQM. */
    obl_ecl2equ_vec(et.mobl, time, ecm, eqm);

    /* Add nutation to convert ECM to true equatorial coordinates of date (EQD). */
    nutation(eqm, &time, FROM_2000, eqd);

    /* Convert back to ecliptic, this time in true equinox of date (ECT). */
    eclip = RotateEquatorialToEcliptic(eqd, DEG2RAD * et.tobl, time);

    /* Package the return value. */
    /* CalcMoon() already set sphere.dist to the correct value. */
    sphere.status = eclip.status;
    sphere.lat = eclip.elat;
    sphere.lon = eclip.elon;
    return sphere;
}


/**
 * @brief Calculates equatorial geocentric position and velocity of the Moon at a given time.
 *
 * Given a time of observation, calculates the Moon's position and velocity vectors.
 * The position and velocity are of the Moon's center relative to the Earth's center.
 * The position (x, y, z) components are expressed in AU (astronomical units).
 * The velocity (vx, vy, vz) components are expressed in AU/day.
 * The coordinates are oriented with respect to the Earth's equator at the J2000 epoch.
 * In Astronomy Engine, this orientation is called EQJ.
 *
 * If you need the Moon's position only, and not its velocity,
 * it is much more efficient to use #Astronomy_GeoMoon instead.
 *
 * @param time  The date and time for which to calculate the Moon's position and velocity.
 * @return The Moon's position and velocity vectors in J2000 equatorial coordinates (EQJ).
 */
astro_state_vector_t Astronomy_GeoMoonState(astro_time_t time)
{
    /*
        This is a hack, because trying to figure out how to derive a time
        derivative for CalcMoon() would be extremely painful!
        Calculate just before and just after the given time.
        Average to find position, subtract to find velocity.
    */
    const double dt = 1.0e-5;   /* 0.864 seconds */
    astro_vector_t r1, r2;
    astro_time_t t1, t2;
    astro_state_vector_t s;

    t1 = Astronomy_AddDays(time, -dt);
    t2 = Astronomy_AddDays(time, +dt);

    r1 = Astronomy_GeoMoon(t1);
    r2 = Astronomy_GeoMoon(t2);

    /* The desired position is the average of the two calculated positions. */
    s.x = (r1.x + r2.x) / 2;
    s.y = (r1.y + r2.y) / 2;
    s.z = (r1.z + r2.z) / 2;

    /* The difference of the position vectors divided by the time span gives the velocity vector. */
    s.vx = (r2.x - r1.x) / (2 * dt);
    s.vy = (r2.y - r1.y) / (2 * dt);
    s.vz = (r2.z - r1.z) / (2 * dt);
    s.t = time;
    s.status = ASTRO_SUCCESS;

    return s;
}


/**
 * @brief Calculates the geocentric position and velocity of the Earth/Moon barycenter.
 *
 * Given a time of observation, calculates the geocentric position and velocity vectors
 * of the Earth/Moon barycenter (EMB).
 * The position (x, y, z) components are expressed in AU (astronomical units).
 * The velocity (vx, vy, vz) components are expressed in AU/day.
 * The coordinates are oriented with respect to the Earth's equator at the J2000 epoch.
 * In Astronomy Engine, this orientation is called EQJ.
 *
 * @param time  The date and time for which to calculate the EMB vectors.
 * @return The EMB's position and velocity vectors in geocentric J2000 equatorial coordinates.
 */
astro_state_vector_t Astronomy_GeoEmbState(astro_time_t time)
{
    astro_state_vector_t s = Astronomy_GeoMoonState(time);
    const double d = 1.0 + EARTH_MOON_MASS_RATIO;
    s.x /= d;
    s.y /= d;
    s.z /= d;
    s.vx /= d;
    s.vy /= d;
    s.vz /= d;
    return s;
}


/**
 * @brief Calculates the Moon's libration angles at a given moment in time.
 *
 * Libration is an observed back-and-forth wobble of the portion of the
 * Moon visible from the Earth. It is caused by the imperfect tidal locking
 * of the Moon's fixed rotation rate, compared to its variable angular speed
 * of orbit around the Earth.
 *
 * This function calculates a pair of perpendicular libration angles,
 * one representing rotation of the Moon in ecliptic longitude `elon`, the other
 * in ecliptic latitude `elat`, both relative to the Moon's mean Earth-facing position.
 *
 * This function also returns the geocentric position of the Moon
 * expressed in ecliptic longitude `mlon`, ecliptic latitude `mlat`, the
 * distance `dist_km` between the centers of the Earth and Moon expressed in kilometers,
 * and the apparent angular diameter of the Moon `diam_deg`.
 *
 * @param time  The date and time for which to calculate libration angles.
 * @return The Moon's ecliptic position and libration angles as seen from the Earth.
 */
astro_libration_t Astronomy_Libration(astro_time_t time)
{
    astro_libration_t lib;
    double t, t2, t3, t4;
    double f, omega, w, a, ldash, ldash2, bdash, bdash2;
    double k1, k2, m, mdash, d, e, rho, sigma, tau;
    const double sin_I = sin(MOON_AXIS_INCLINATION_RADIANS);
    const double cos_I = cos(MOON_AXIS_INCLINATION_RADIANS);

    t = time.tt / 36525.0;
    t2 = t * t;
    t3 = t2 * t;
    t4 = t2 * t2;

    double mlon;    /* Moon's ecliptic longitude in radians. */
    double mlat;    /* Moon's ecliptic latitude in radians. */
    CalcMoon(t, &mlon, &mlat, &lib.dist_km);
    lib.mlon = RAD2DEG * mlon;
    lib.mlat = RAD2DEG * mlat;
    lib.dist_km *= KM_PER_AU;
    lib.diam_deg = (2.0 * RAD2DEG) * atan(MOON_MEAN_RADIUS_KM / sqrt(lib.dist_km*lib.dist_km - MOON_MEAN_RADIUS_KM*MOON_MEAN_RADIUS_KM));

    /* Moon's argument of latitude in radians. */
    f = DEG2RAD * NormalizeLongitude(93.2720950 + 483202.0175233*t - 0.0036539*t2 - t3/3526000 + t4/863310000);

    /* Moon's ascending node's mean longitude in radians. */
    omega = DEG2RAD * NormalizeLongitude(125.0445479 - 1934.1362891*t + 0.0020754*t2 + t3/467441 - t4/60616000);

    /* Sun's mean anomaly. */
    m = DEG2RAD * NormalizeLongitude(357.5291092 + 35999.0502909*t - 0.0001536*t2 + t3/24490000);

    /* Moon's mean anomaly. */
    mdash = DEG2RAD * NormalizeLongitude(134.9633964 + 477198.8675055*t + 0.0087414*t2 + t3/69699 - t4/14712000);

    /* Moon's mean elongation. */
    d = DEG2RAD * NormalizeLongitude(297.8501921 + 445267.1114034*t - 0.0018819*t2 + t3/545868 - t4/113065000);

    /* Eccentricity of the Earth's orbit. */
    e = 1.0 - 0.002516*t - 0.0000074*t2;

    /* Optical librations */
    w = mlon - omega;
    a = atan2(sin(w)*cos(mlat)*cos_I - sin(mlat)*sin_I, cos(w)*cos(mlat));
    ldash = LongitudeOffset(RAD2DEG * (a - f));
    bdash = asin(-sin(w)*cos(mlat)*sin_I - sin(mlat)*cos_I);

    /* Physical librations */
    k1 = DEG2RAD*(119.75 + 131.849*t);
    k2 = DEG2RAD*(72.56 + 20.186*t);

    rho = (
        -0.02752*cos(mdash) +
        -0.02245*sin(f) +
        +0.00684*cos(mdash - 2*f) +
        -0.00293*cos(2*f) +
        -0.00085*cos(2*f - 2*d) +
        -0.00054*cos(mdash - 2*d) +
        -0.00020*sin(mdash + f) +
        -0.00020*cos(mdash + 2*f) +
        -0.00020*cos(mdash - f) +
        +0.00014*cos(mdash + 2*f - 2*d)
    );

    sigma = (
        -0.02816*sin(mdash) +
        +0.02244*cos(f) +
        -0.00682*sin(mdash - 2*f) +
        -0.00279*sin(2*f) +
        -0.00083*sin(2*f - 2*d) +
        +0.00069*sin(mdash - 2*d) +
        +0.00040*cos(mdash + f) +
        -0.00025*sin(2*mdash) +
        -0.00023*sin(mdash + 2*f) +
        +0.00020*cos(mdash - f) +
        +0.00019*sin(mdash - f) +
        +0.00013*sin(mdash + 2*f - 2*d) +
        -0.00010*cos(mdash - 3*f)
    );

    tau = (
        +0.02520*e*sin(m) +
        +0.00473*sin(2*mdash - 2*f) +
        -0.00467*sin(mdash) +
        +0.00396*sin(k1) +
        +0.00276*sin(2*mdash - 2*d) +
        +0.00196*sin(omega) +
        -0.00183*cos(mdash - f) +
        +0.00115*sin(mdash - 2*d) +
        -0.00096*sin(mdash - d) +
        +0.00046*sin(2*f - 2*d) +
        -0.00039*sin(mdash - f) +
        -0.00032*sin(mdash - m - d) +
        +0.00027*sin(2*mdash - m - 2*d) +
        +0.00023*sin(k2) +
        -0.00014*sin(2*d) +
        +0.00014*cos(2*mdash - 2*f) +
        -0.00012*sin(mdash - 2*f) +
        -0.00012*sin(2*mdash) +
        +0.00011*sin(2*mdash - 2*m - 2*d)
    );

    ldash2 = -tau + (rho*cos(a) + sigma*sin(a))*tan(bdash);
    bdash *= RAD2DEG;
    bdash2 = sigma*cos(a) - rho*sin(a);

    lib.elon = ldash + ldash2;
    lib.elat = bdash + bdash2;

    return lib;
}


/*------------------ VSOP ------------------*/

/** @cond DOXYGEN_SKIP */
typedef struct
{
    double amplitude;
    double phase;
    double frequency;
}
vsop_term_t;

typedef struct
{
    int nterms;
    const vsop_term_t *term;
}
vsop_series_t;

typedef struct
{
    int nseries;
    const vsop_series_t *series;
}
vsop_formula_t;

typedef struct
{
    const vsop_formula_t formula[3];
}
vsop_model_t;

typedef struct
{
    double mu;
    double al[2];
    vsop_series_t a;
    vsop_series_t l;
    vsop_series_t z;
    vsop_series_t zeta;
}
jupiter_moon_t;
/** @endcond */

static const vsop_term_t vsop_lon_Mercury_0[] =
{
    { 4.40250710144, 0.00000000000, 0.00000000000 },
    { 0.40989414977, 1.48302034195, 26087.90314157420 },
    { 0.05046294200, 4.47785489551, 52175.80628314840 },
    { 0.00855346844, 1.16520322459, 78263.70942472259 },
    { 0.00165590362, 4.11969163423, 104351.61256629678 },
    { 0.00034561897, 0.77930768443, 130439.51570787099 },
    { 0.00007583476, 3.71348404924, 156527.41884944518 }
};

static const vsop_term_t vsop_lon_Mercury_1[] =
{
    { 26087.90313685529, 0.00000000000, 0.00000000000 },
    { 0.01131199811, 6.21874197797, 26087.90314157420 },
    { 0.00292242298, 3.04449355541, 52175.80628314840 },
    { 0.00075775081, 6.08568821653, 78263.70942472259 },
    { 0.00019676525, 2.80965111777, 104351.61256629678 }
};

static const vsop_series_t vsop_lon_Mercury[] =
{
    { 7, vsop_lon_Mercury_0 },
    { 5, vsop_lon_Mercury_1 }
};

static const vsop_term_t vsop_lat_Mercury_0[] =
{
    { 0.11737528961, 1.98357498767, 26087.90314157420 },
    { 0.02388076996, 5.03738959686, 52175.80628314840 },
    { 0.01222839532, 3.14159265359, 0.00000000000 },
    { 0.00543251810, 1.79644363964, 78263.70942472259 },
    { 0.00129778770, 4.83232503958, 104351.61256629678 },
    { 0.00031866927, 1.58088495658, 130439.51570787099 },
    { 0.00007963301, 4.60972126127, 156527.41884944518 }
};

static const vsop_term_t vsop_lat_Mercury_1[] =
{
    { 0.00274646065, 3.95008450011, 26087.90314157420 },
    { 0.00099737713, 3.14159265359, 0.00000000000 }
};

static const vsop_series_t vsop_lat_Mercury[] =
{
    { 7, vsop_lat_Mercury_0 },
    { 2, vsop_lat_Mercury_1 }
};

static const vsop_term_t vsop_rad_Mercury_0[] =
{
    { 0.39528271651, 0.00000000000, 0.00000000000 },
    { 0.07834131818, 6.19233722598, 26087.90314157420 },
    { 0.00795525558, 2.95989690104, 52175.80628314840 },
    { 0.00121281764, 6.01064153797, 78263.70942472259 },
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
    { 0.00135134092, 3.37220609835, 39.61750834610 },
    { 0.00007571796, 1.07149207335, 388.46515523820 }
};

static const vsop_series_t vsop_rad_Neptune[] =
{
    { 12, vsop_rad_Neptune_0 }
};

;

/** @cond DOXYGEN_SKIP */
#define VSOPFORMULA(x)    { ASTRO_ARRAYSIZE(x), x }
/** @endcond */
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
