Areeeeen/OW_Signalscope_Planet_Finder/Tools/ICM20948_calibration/ICM20948_calibration.ino

#include <Wire.h>
#include <ICM20948_WE.h>
#define ICM20948_ADDR 0x69

ICM20948_WE myIMU = ICM20948_WE(ICM20948_ADDR);

void setup() {
  //delay(2000); // maybe needed for some MCUs, in particular for startup after power off
  Wire.begin();
  Serial.begin(115200);
  while(!Serial) {}
  
  if(!myIMU.init()){
    Serial.println("ICM20948 does not respond");
  }
  else{
    Serial.println("ICM20948 is connected");
  }

  /*  This is a method to calibrate. You have to determine the minimum and maximum 
   *  raw acceleration values of the axes determined in the range +/- 2 g. 
   *  You call the function as follows: setAccOffsets(xMin,xMax,yMin,yMax,zMin,zMax);
   *  The parameters are floats. 
   *  The calibration changes the slope / ratio of raw accleration vs g. The zero point is 
   *  set as (min + max)/2.
   */
  myIMU.setAccOffsets(-16330.0, 16450.0, -16600.0, 16180.0, -16520.0, 16690.0);
    
  /*  The gyroscope data is not zero, even if you don't move the ICM20948. 
   *  To start at zero, you can apply offset values. These are the gyroscope raw values you obtain
   *  using the +/- 250 degrees/s range. 
   *  Use either autoOffset or setGyrOffsets, not both.
   */
  myIMU.setGyrOffsets(-115.0, 130.0, 105.0);
    
  /*  ICM20948_ACC_RANGE_2G      2 g   (default)
   *  ICM20948_ACC_RANGE_4G      4 g
   *  ICM20948_ACC_RANGE_8G      8 g   
   *  ICM20948_ACC_RANGE_16G    16 g
   */
  myIMU.setAccRange(ICM20948_ACC_RANGE_2G); // highest res for calibration
  
  /*  Choose a level for the Digital Low Pass Filter or switch it off.  
   *  ICM20948_DLPF_0, ICM20948_DLPF_2, ...... ICM20948_DLPF_7, ICM20948_DLPF_OFF 
   *  
   *  IMPORTANT: This needs to be ICM20948_DLPF_7 if DLPF is used in cycle mode!
   *  
   *  DLPF       3dB Bandwidth [Hz]      Output Rate [Hz]
   *    0              246.0               1125/(1+ASRD) 
   *    1              246.0               1125/(1+ASRD)
   *    2              111.4               1125/(1+ASRD)
   *    3               50.4               1125/(1+ASRD)
   *    4               23.9               1125/(1+ASRD)
   *    5               11.5               1125/(1+ASRD)
   *    6                5.7               1125/(1+ASRD) 
   *    7              473.0               1125/(1+ASRD)
   *    OFF           1209.0               4500
   *    
   *    ASRD = Accelerometer Sample Rate Divider (0...4095)
   *    You achieve lowest noise using level 6  
   */
  myIMU.setAccDLPF(ICM20948_DLPF_6); // lowest noise for calibration   
  
  /*  ICM20948_GYRO_RANGE_250       250 degrees per second (default)
   *  ICM20948_GYRO_RANGE_500       500 degrees per second
   *  ICM20948_GYRO_RANGE_1000     1000 degrees per second
   *  ICM20948_GYRO_RANGE_2000     2000 degrees per second
   */
  myIMU.setGyrRange(ICM20948_GYRO_RANGE_250); //highest resolution for calibration
  
  /*  Choose a level for the Digital Low Pass Filter or switch it off. 
   *  ICM20948_DLPF_0, ICM20948_DLPF_2, ...... ICM20948_DLPF_7, ICM20948_DLPF_OFF 
   *  
   *  DLPF       3dB Bandwidth [Hz]      Output Rate [Hz]
   *    0              196.6               1125/(1+GSRD) 
   *    1              151.8               1125/(1+GSRD)
   *    2              119.5               1125/(1+GSRD)
   *    3               51.2               1125/(1+GSRD)
   *    4               23.9               1125/(1+GSRD)
   *    5               11.6               1125/(1+GSRD)
   *    6                5.7               1125/(1+GSRD) 
   *    7              361.4               1125/(1+GSRD)
   *    OFF          12106.0               9000
   *    
   *    GSRD = Gyroscope Sample Rate Divider (0...255)
   *    You achieve lowest noise using level 6  
   */
  myIMU.setGyrDLPF(ICM20948_DLPF_6); // lowest noise for calibration
  
  /*  Choose a level for the Digital Low Pass Filter. 
   *  ICM20948_DLPF_0, ICM20948_DLPF_2, ...... ICM20948_DLPF_7, ICM20948_DLPF_OFF 
   *  
   *  DLPF          Bandwidth [Hz]      Output Rate [Hz]
   *    0             7932.0                    9
   *    1              217.9                 1125
   *    2              123.5                 1125
   *    3               65.9                 1125
   *    4               34.1                 1125
   *    5               17.3                 1125
   *    6                8.8                 1125
   *    7             7932.0                    9
   *                 
   *    
   *    GSRD = Gyroscope Sample Rate Divider (0...255)
   *    You achieve lowest noise using level 6  
   */
  myIMU.setTempDLPF(ICM20948_DLPF_6); // lowest noise for calibration
}

void loop() {
  xyzFloat accRaw;
  xyzFloat gyrRaw;
  xyzFloat corrAccRaw;
  xyzFloat corrGyrRaw;
  xyzFloat gVal;
  myIMU.readSensor();
  myIMU.getAccRawValues(&accRaw);
  myIMU.getGyrRawValues(&gyrRaw);
  myIMU.getCorrectedAccRawValues(&corrAccRaw);
  myIMU.getCorrectedGyrRawValues(&corrGyrRaw);
  myIMU.getGValues(&gVal);
  
  Serial.println("Acceleration raw values without offset:");
  Serial.print(accRaw.x);
  Serial.print("   ");
  Serial.print(accRaw.y);
  Serial.print("   ");
  Serial.println(accRaw.z);

  Serial.println("Gyroscope raw values without offset:");
  Serial.print(gyrRaw.x);
  Serial.print("   ");
  Serial.print(gyrRaw.y);
  Serial.print("   ");
  Serial.println(gyrRaw.z);

  Serial.println("Acceleration raw values with offset:");
  Serial.print(corrAccRaw.x);
  Serial.print("   ");
  Serial.print(corrAccRaw.y);
  Serial.print("   ");
  Serial.println(corrAccRaw.z);

  Serial.println("Gyroscope raw values with offset:");
  Serial.print(corrGyrRaw.x);
  Serial.print("   ");
  Serial.print(corrGyrRaw.y);
  Serial.print("   ");
  Serial.println(corrGyrRaw.z);

  Serial.println("g-values, based on corrected raws (x,y,z):");
  Serial.print(gVal.x);
  Serial.print("   ");
  Serial.print(gVal.y);
  Serial.print("   ");
  Serial.println(gVal.z);


  Serial.println("********************************************");

  delay(500);
}
